Andrew-Sherwin/ECE445/Course Files/KiCAD Files/Extra Credit Video/Extra Credit Video.docx

1. Introduction/Explanation of project goal/problem statement
  a. Skit with girl saying its too humid and/or not humid enough
    i. Wow, its so dry in here
      1. Its about to get more humid later… after I turn on the humidifier *wink*
    ii. Wow its so humid in here
      1. I left the manual humidifier on, and now its 60% humidity in here
2. Highlight key operating concept(s) and features,
  a. App
    i. Manual mode, auto mode
  b. Visual aid
  c. Sensor in box, valve, fan, modular plug, cable
3. Visually demonstrate the functionality and usability of these features by showing all or a part of the device working.
  a. Showing project
4. Pull back the curtain and explain/show the guts of your project including the PCB, and any motors/sensors.
  a. Show PCBs, water level sensor, valve
