Andrew-Sherwin/ECE445/Course Files/Schematics/Block Diagram/ECE445 Block Diagram Rev2.pdf

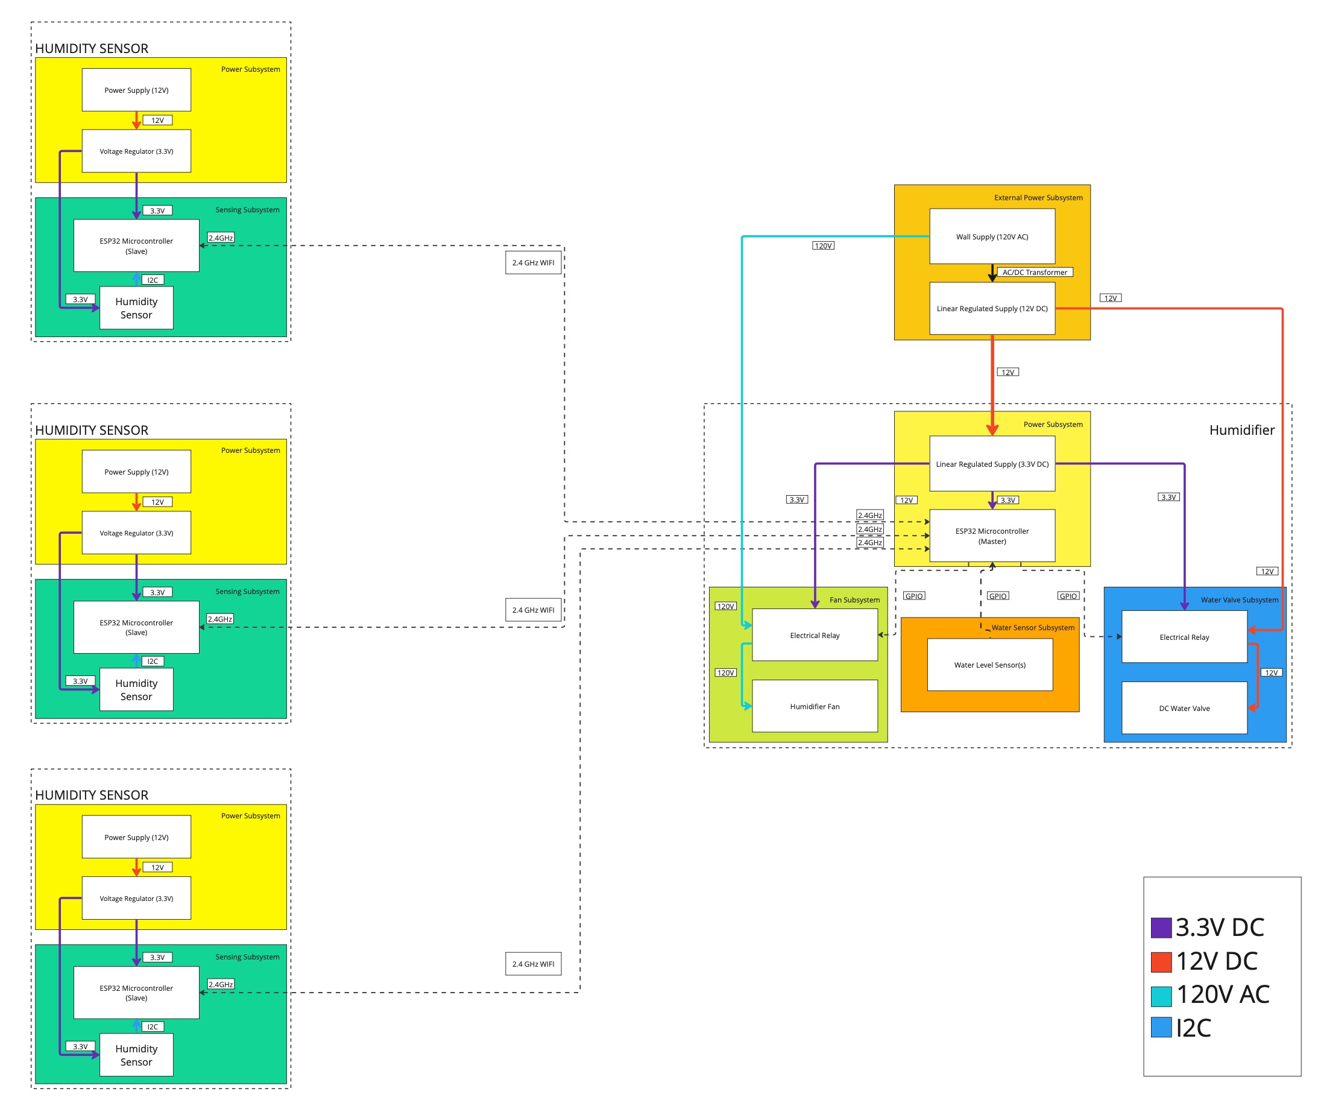
[picture p62: page 1]
