Andrew-Sherwin/ECE445/Course Files/Block Diagram/ECE445 Block Diagram Rev6.pdf

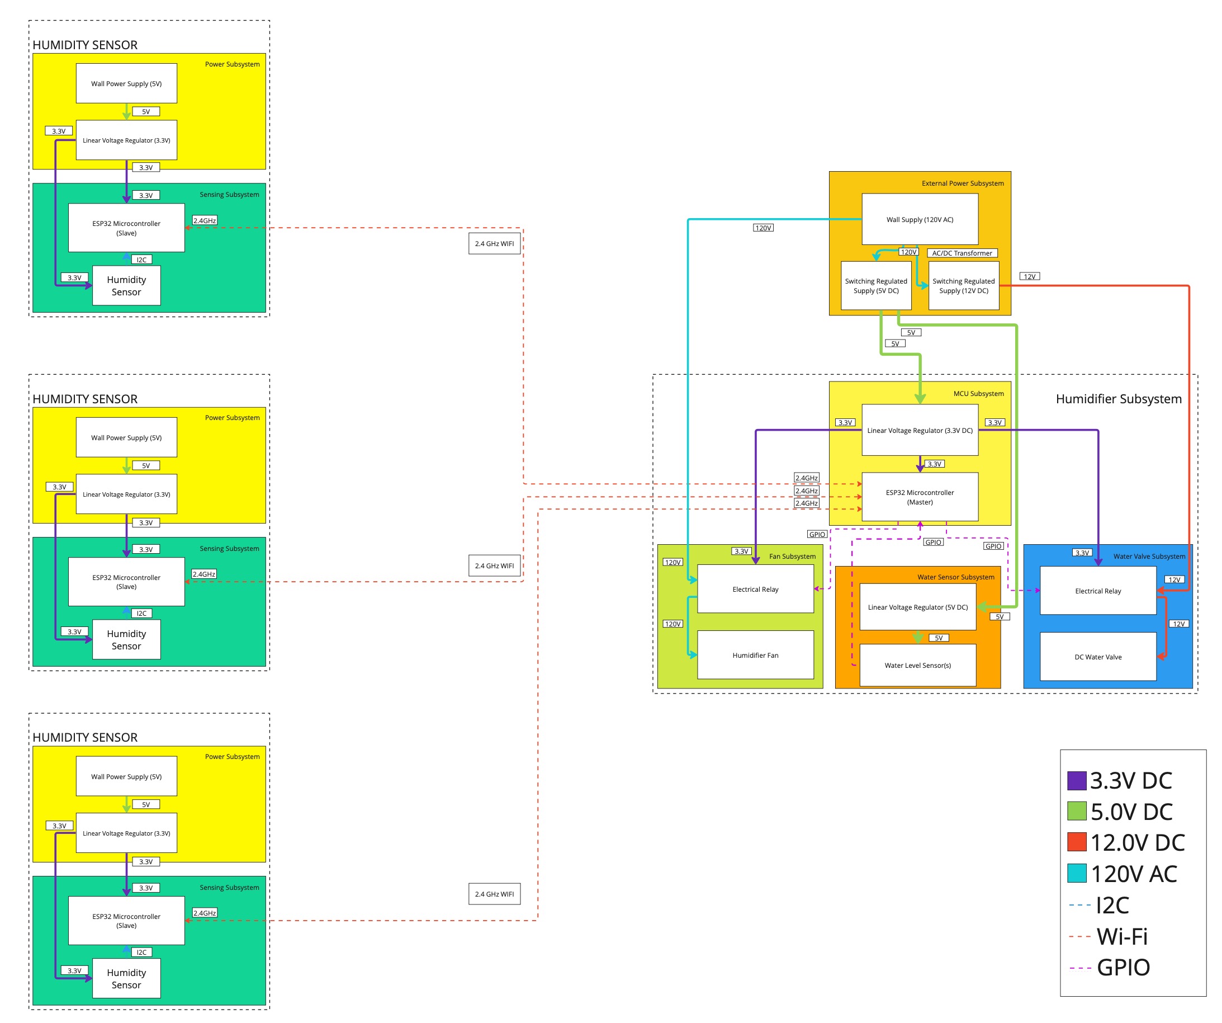
[picture p63: page 1]
