Andrew-Sherwin/ECE445/Course Files/Demonstration/Handout Rev2/Photo ECE445 Demo Handout Rev2.pdf

## Visual Aid


Automatic Humidity Sensing and Water Refilling Cool-Mist Humidifier | 5

Figure 1: Consumer Visual Aid

## Physical Design

Figure 2 – Component Visual Aid

Automatic Humidity Sensing and Water Refilling Cool-Mist Humidifier | 7

# Design

## Block Diagram


Figure 3 – Overall Block Diagram

Automatic Humidity Sensing and Water Refilling Cool-Mist Humidifier | 8


Figure 4 – Humidifier Subsystem Block Diagram (Close-up)

Automatic Humidity Sensing and Water Refilling Cool-Mist Humidifier | 9


Figure 5 – Humidity Sensor Subsystem Block Diagram (Close-up)
