Andrew-Sherwin/ECE445/Course Files/Block Diagram/ECE445 Block Diagram Rev3.pdf

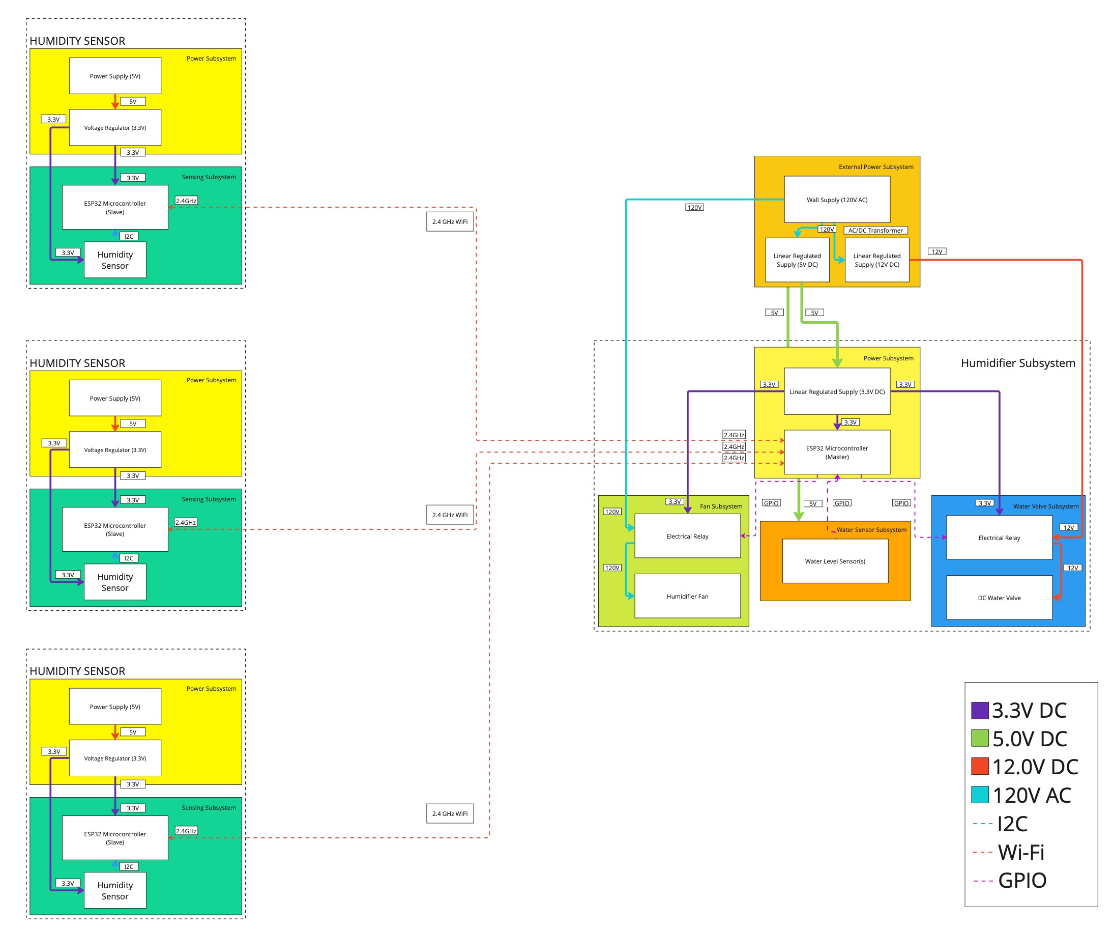
[picture p73: page 1]
