Andrew-Sherwin/ECE445/Course Files/Block Diagram/ECE445 Block Diagram Rev4.pdf

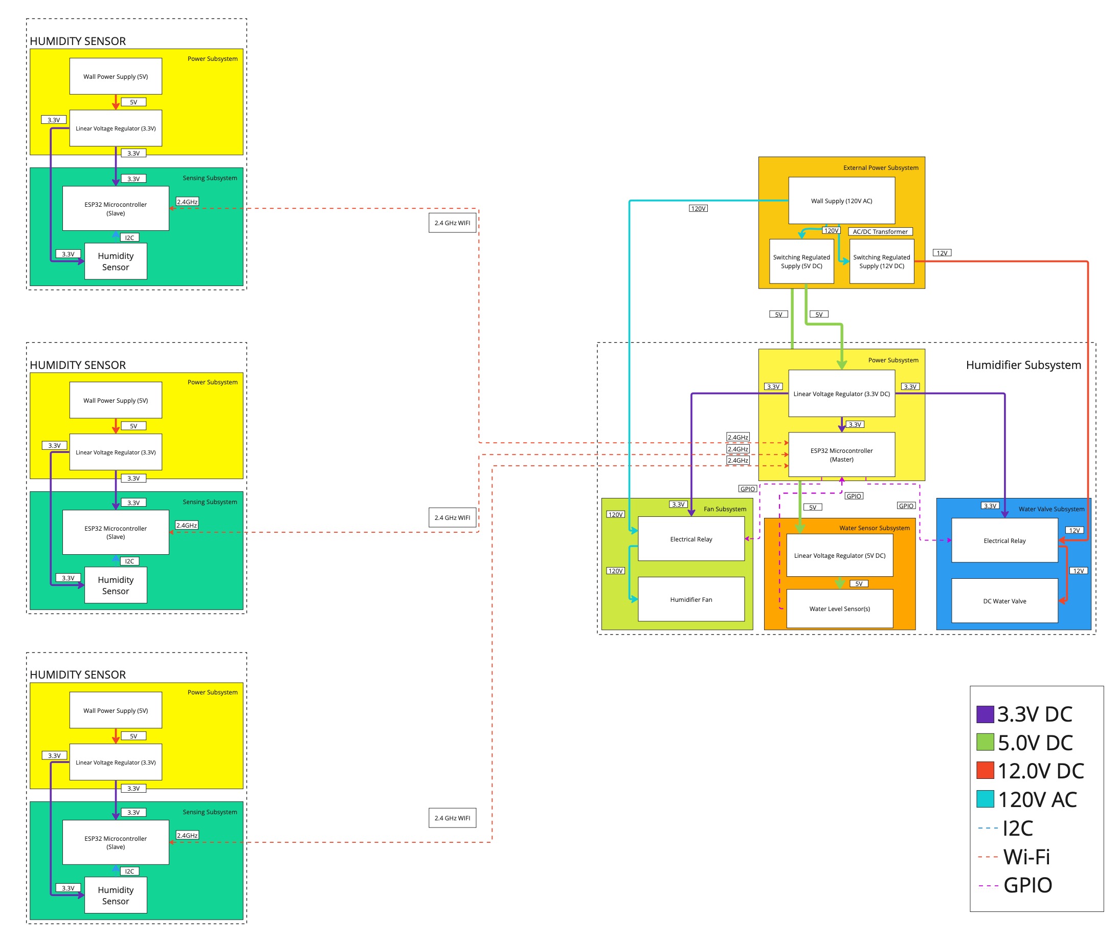
[picture p74: page 1]
