Andrew-Sherwin/ECE445/Course Files/Block Diagram/ECE445 Block Diagram Rev5.pdf

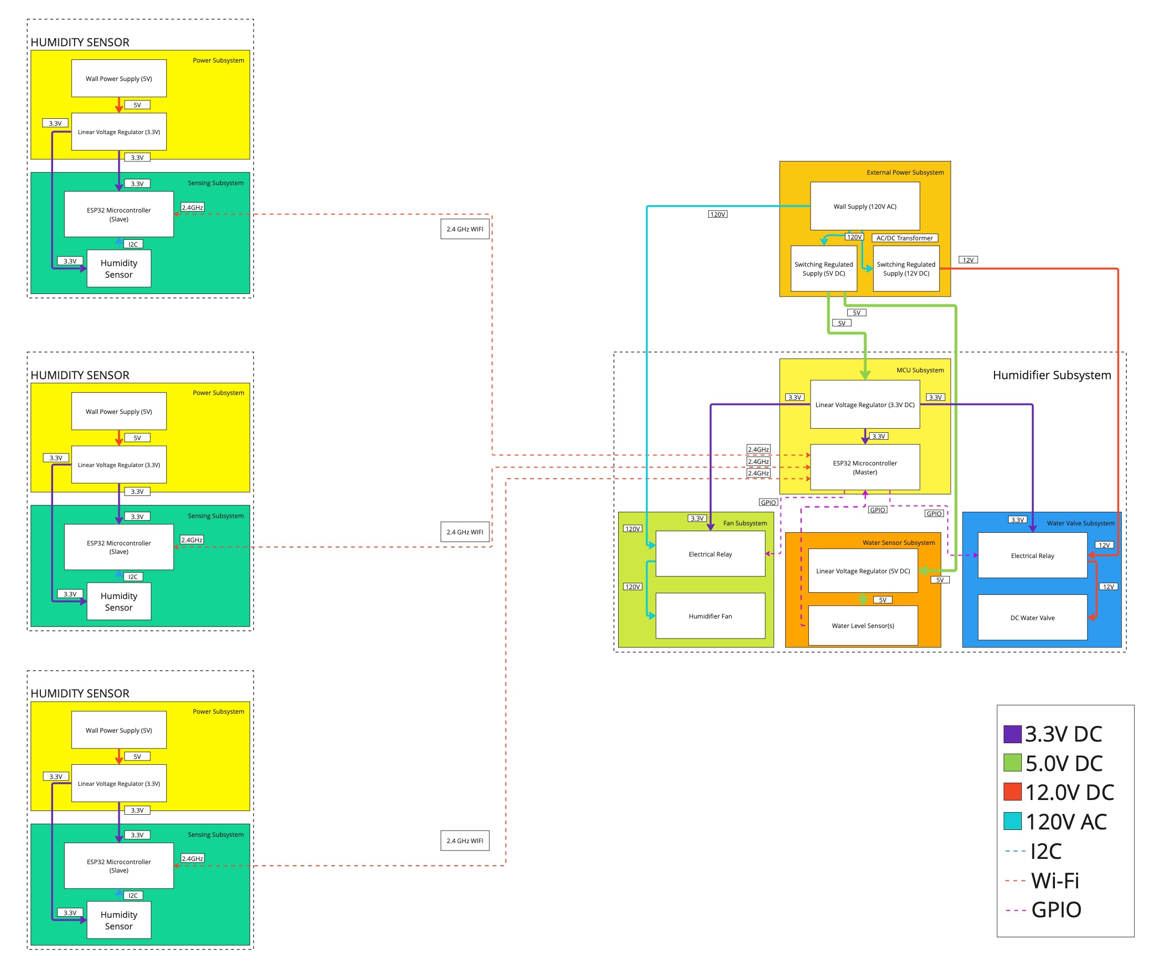
[picture p75: page 1]
