Andrew-Sherwin/ECE445/Course Files/3D Scan/humidifier photo.jpg

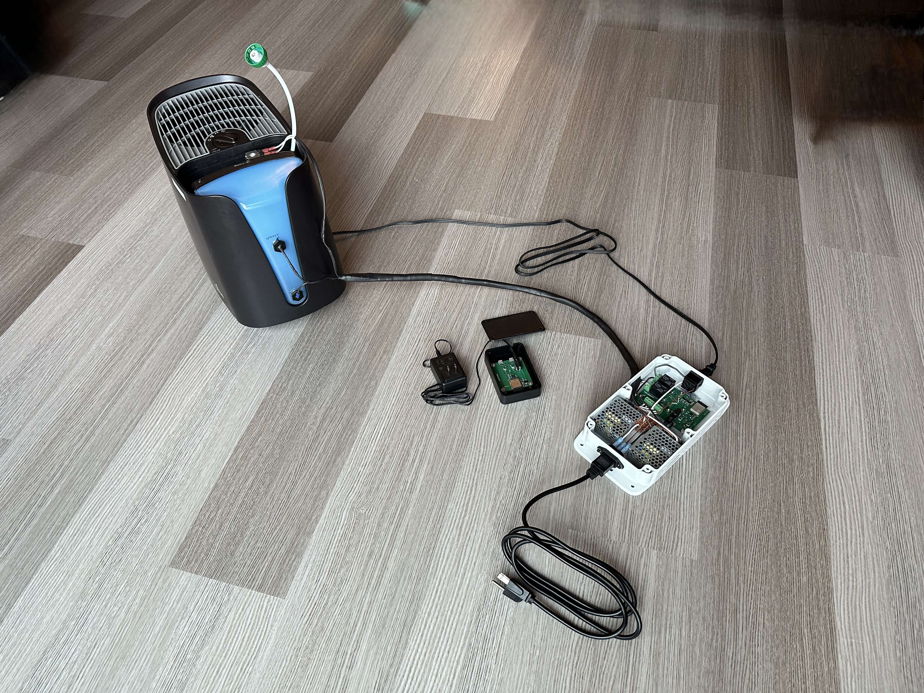
Course Files/3D Scan/humidifier photo.jpg
