Andrew-Sherwin/ECE445/Course Files/Budget/Screenshot 2024-05-01 at 22.21.20.png

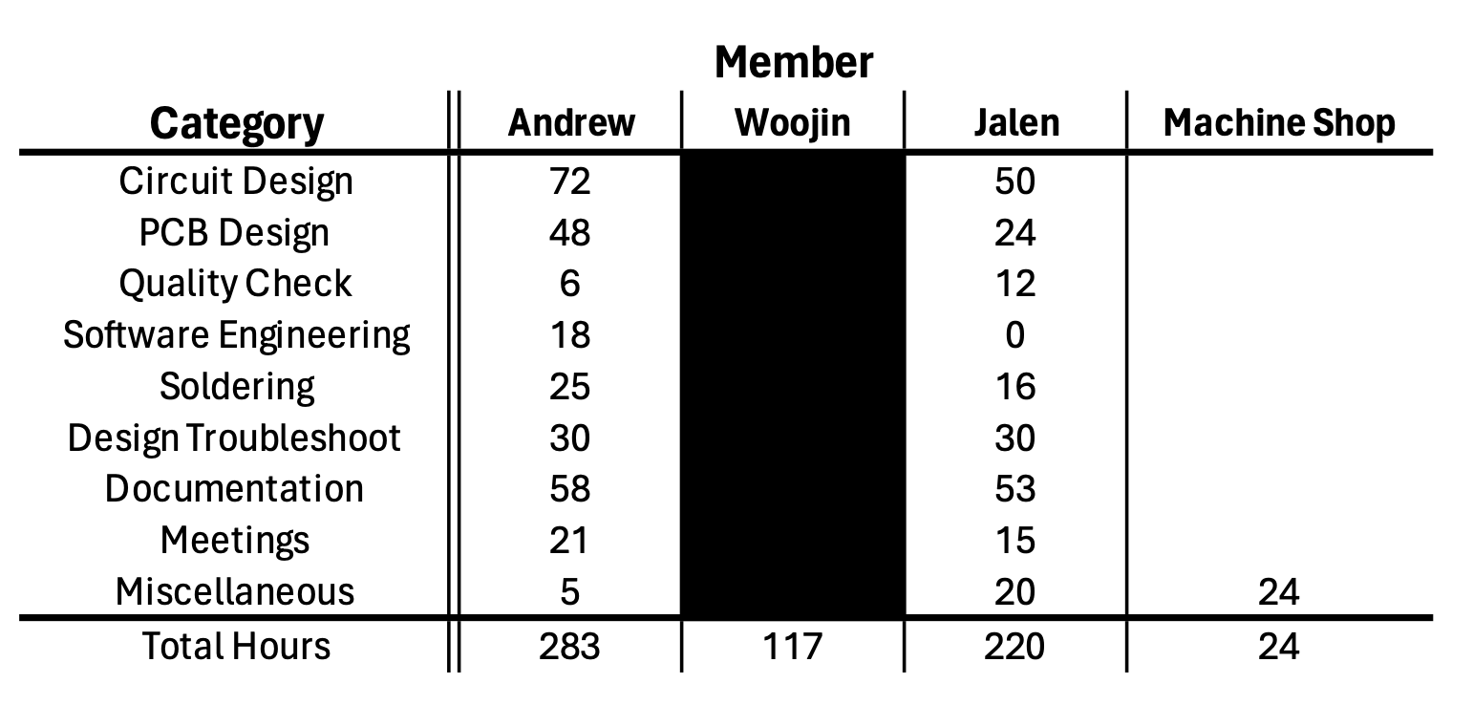
Course Files/Budget/Screenshot 2024-05-01 at 22.21.20.png
