Andrew-Sherwin/ECE445/Course Files/Demonstration/Pictures/5-1.png

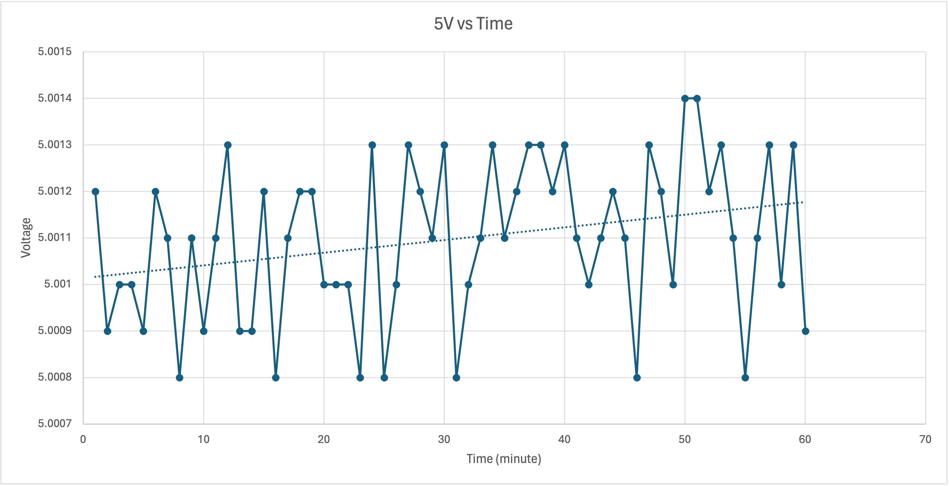
Course Files/Demonstration/Pictures/5-1.png
