Andrew-Sherwin/ECE445/Course Files/Demonstration/Pictures/5-2.png

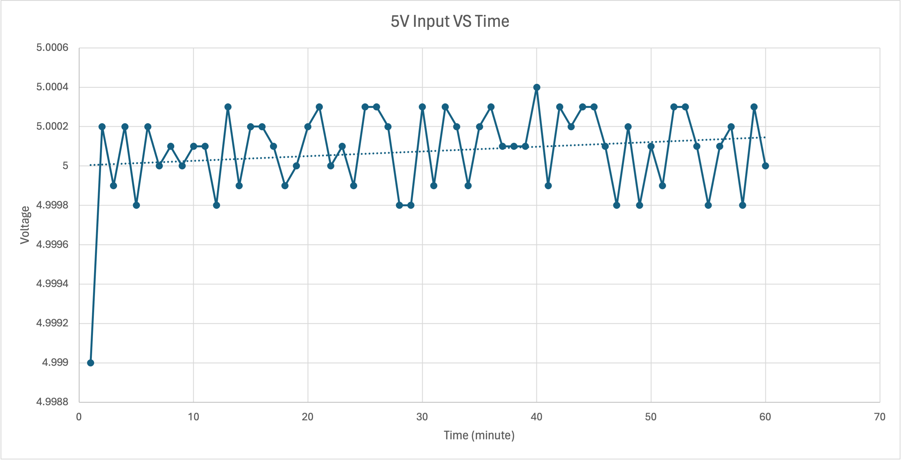
Course Files/Demonstration/Pictures/5-2.png
