Andrew-Sherwin/ECE445/Course Files/Demonstration/Pictures/33-1.png

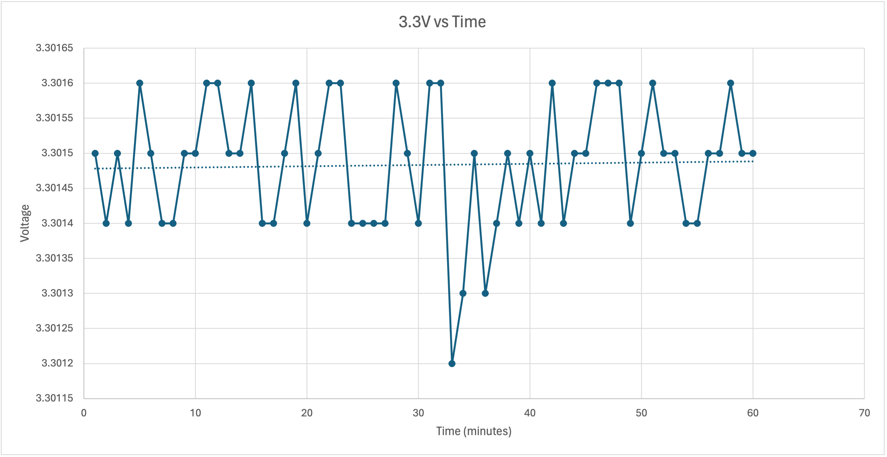
Course Files/Demonstration/Pictures/33-1.png
