Andrew-Sherwin/ECE445/Course Files/Demonstration/Pictures/33-2.png

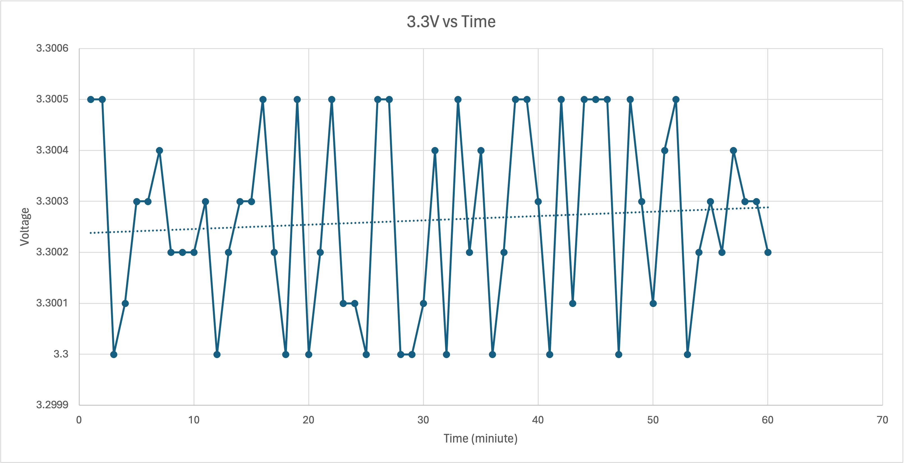
Course Files/Demonstration/Pictures/33-2.png
