Andrew-Sherwin/ECE445/Course Files/Extra Credit Video/Clips/IMG_0042.PNG

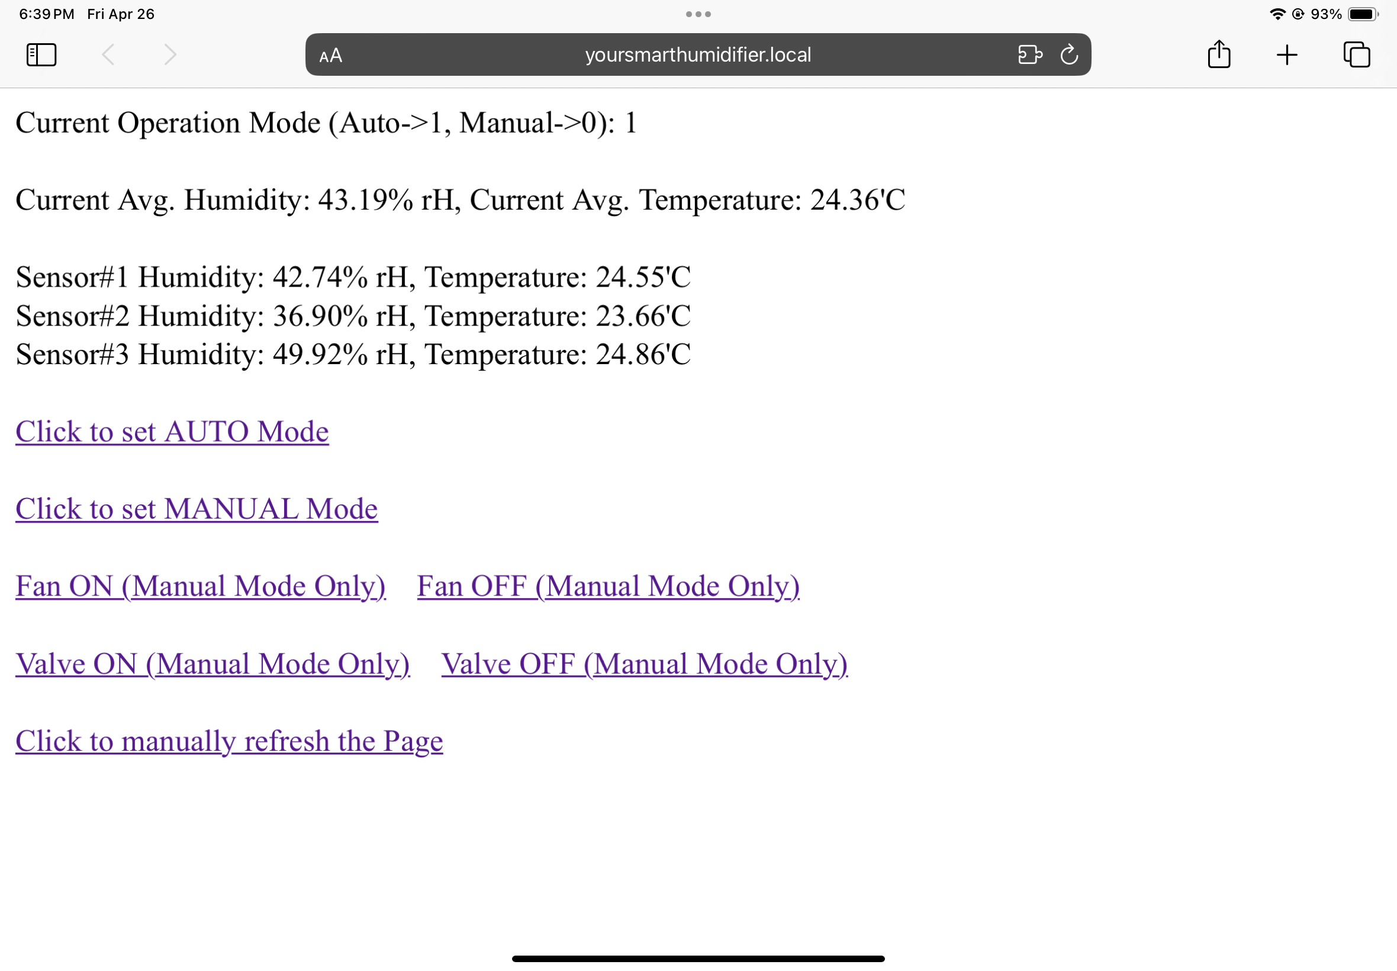
Course Files/Extra Credit Video/Clips/IMG_0042.PNG
