Andrew-Sherwin/ECE445/Course Files/Final Presentation/ebony guest.png

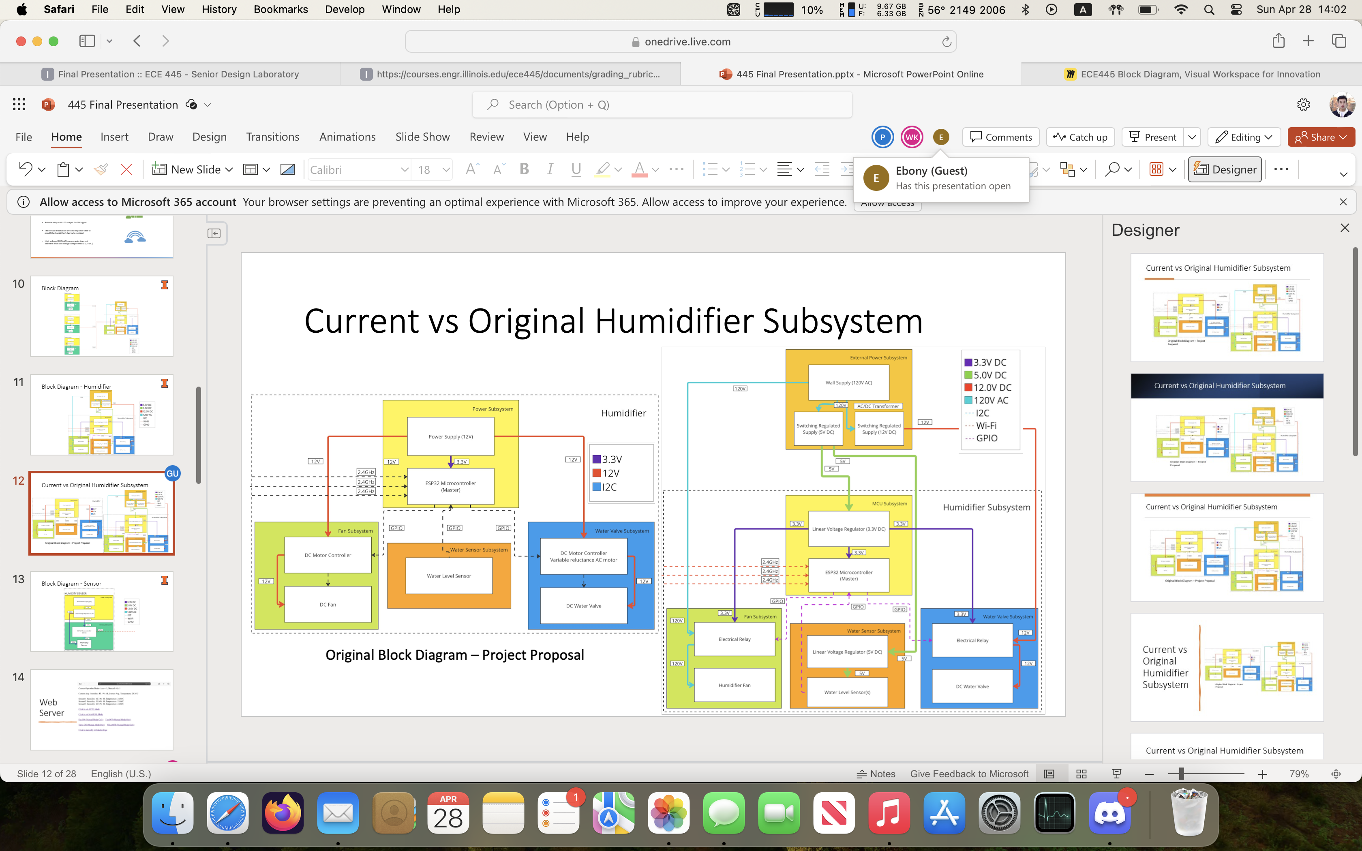
Course Files/Final Presentation/ebony guest.png
