Andrew-Sherwin/ECE445/Course Files/Final Presentation/Temp vs Time 29.1.png

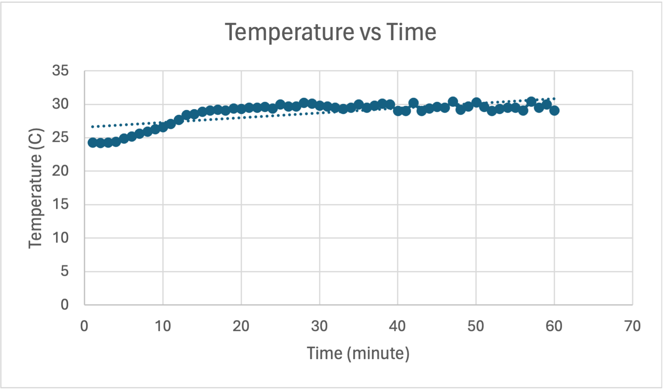
Course Files/Final Presentation/Temp vs Time 29.1.png
