Andrew-Sherwin/ECE445/Course Files/Final Presentation/Temperature vs time 311.png

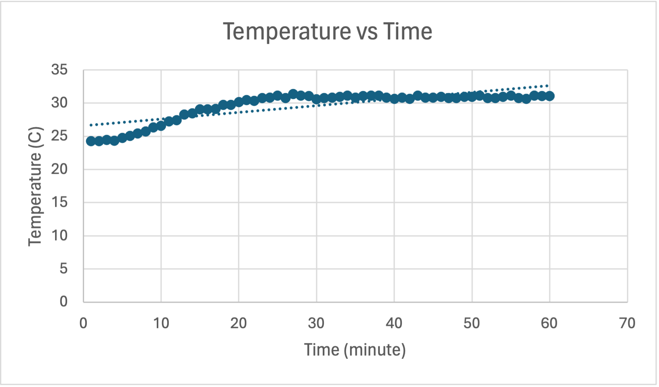
Course Files/Final Presentation/Temperature vs time 311.png
