Andrew-Sherwin/ECE445/Course Files/Final Report/Labor Table.png

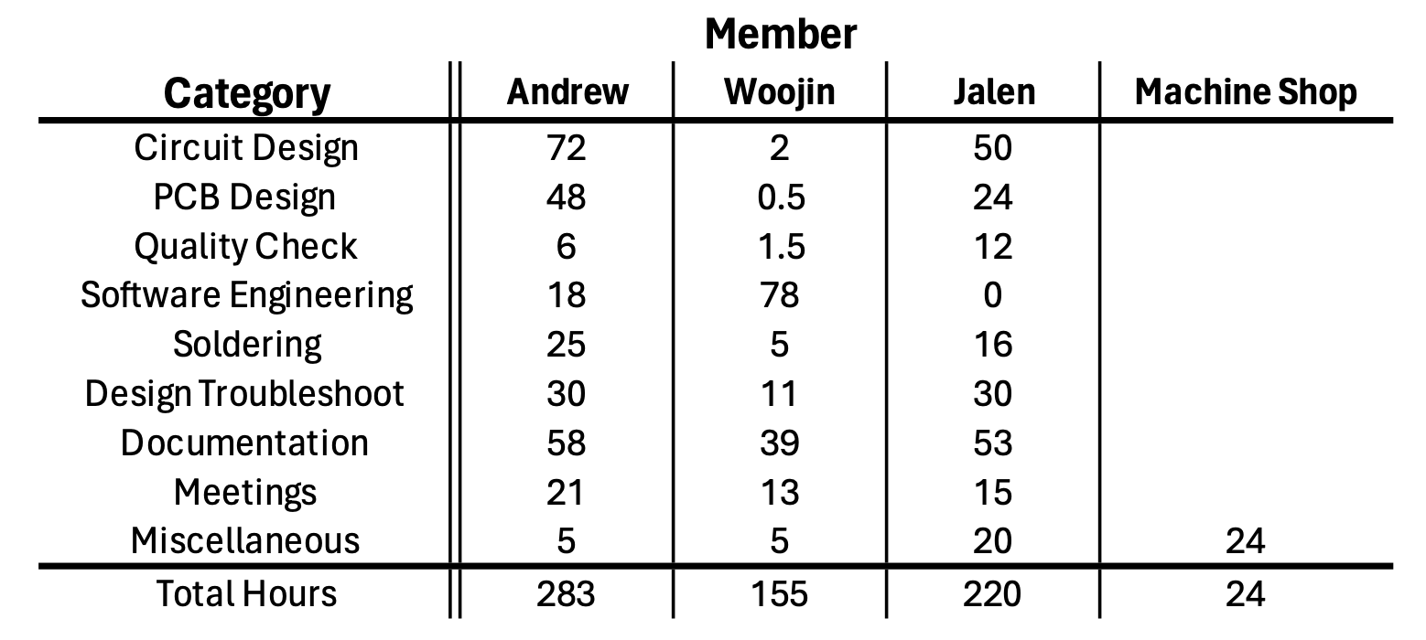
Course Files/Final Report/Labor Table.png
