Andrew-Sherwin/ECE445/Course Files/KiCAD Files/Extra Credit Video/Screenshot 2024-04-26 at 20.52.26.png

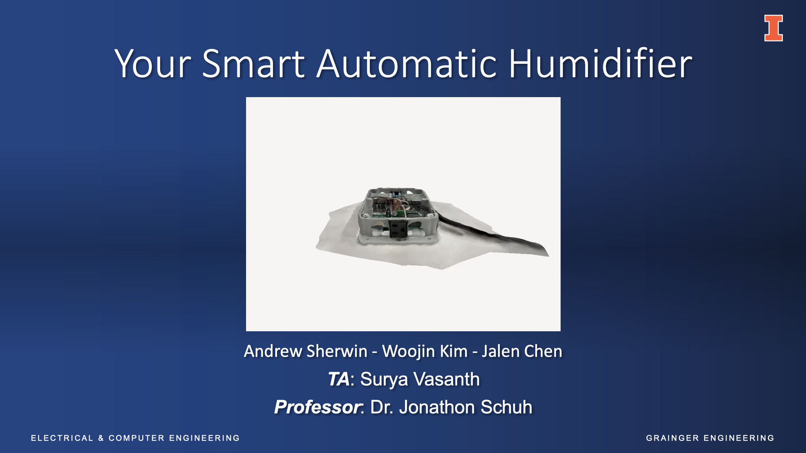
Course Files/KiCAD Files/Extra Credit Video/Screenshot 2024-04-26 at 20.52.26.png
