Andrew-Sherwin/ECE445/Course Files/KiCAD Files/Humidifier Subsystem/Jalen/Jalen kissing.png

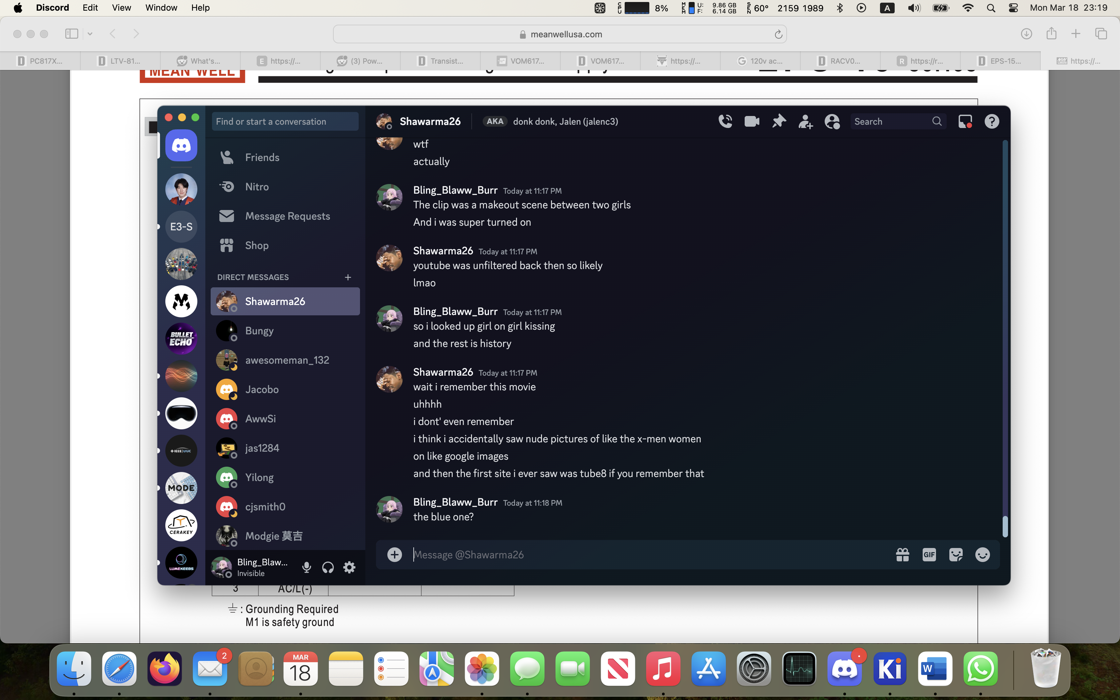
Course Files/KiCAD Files/Humidifier Subsystem/Jalen/Jalen kissing.png
