Andrew-Sherwin/ECE445/Course Files/KiCAD Files/Humidifier Subsystem/Jalen/Screenshot 2024-03-19 at 01.11.47.png

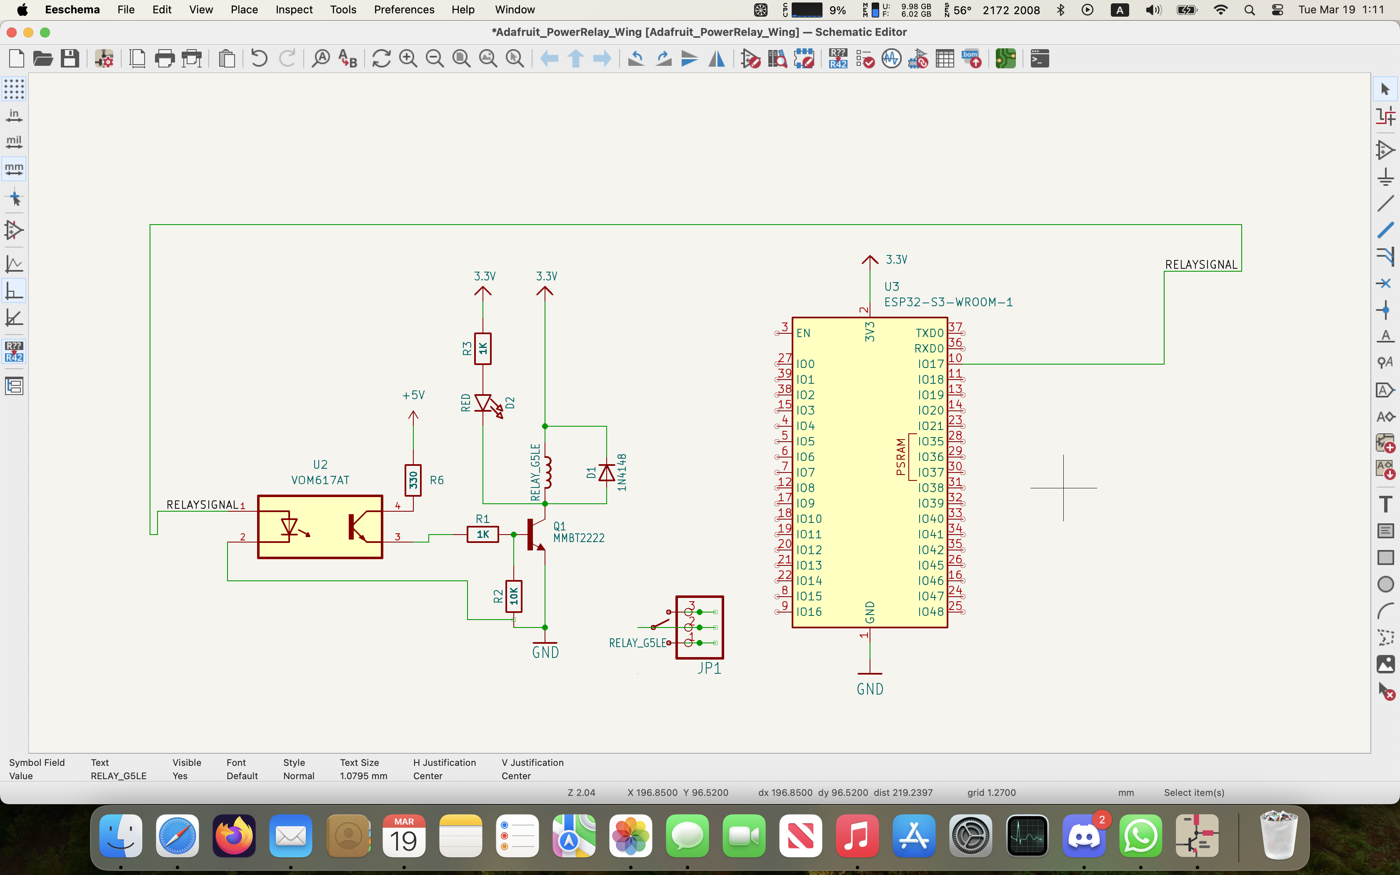
Course Files/KiCAD Files/Humidifier Subsystem/Jalen/Screenshot 2024-03-19 at 01.11.47.png
