Andrew-Sherwin/ECE445/Course Files/KiCAD Files/Humidifier Subsystem/KiCad 7.0/Rev7/Screenshot 2024-03-19 at 15.34.11.png

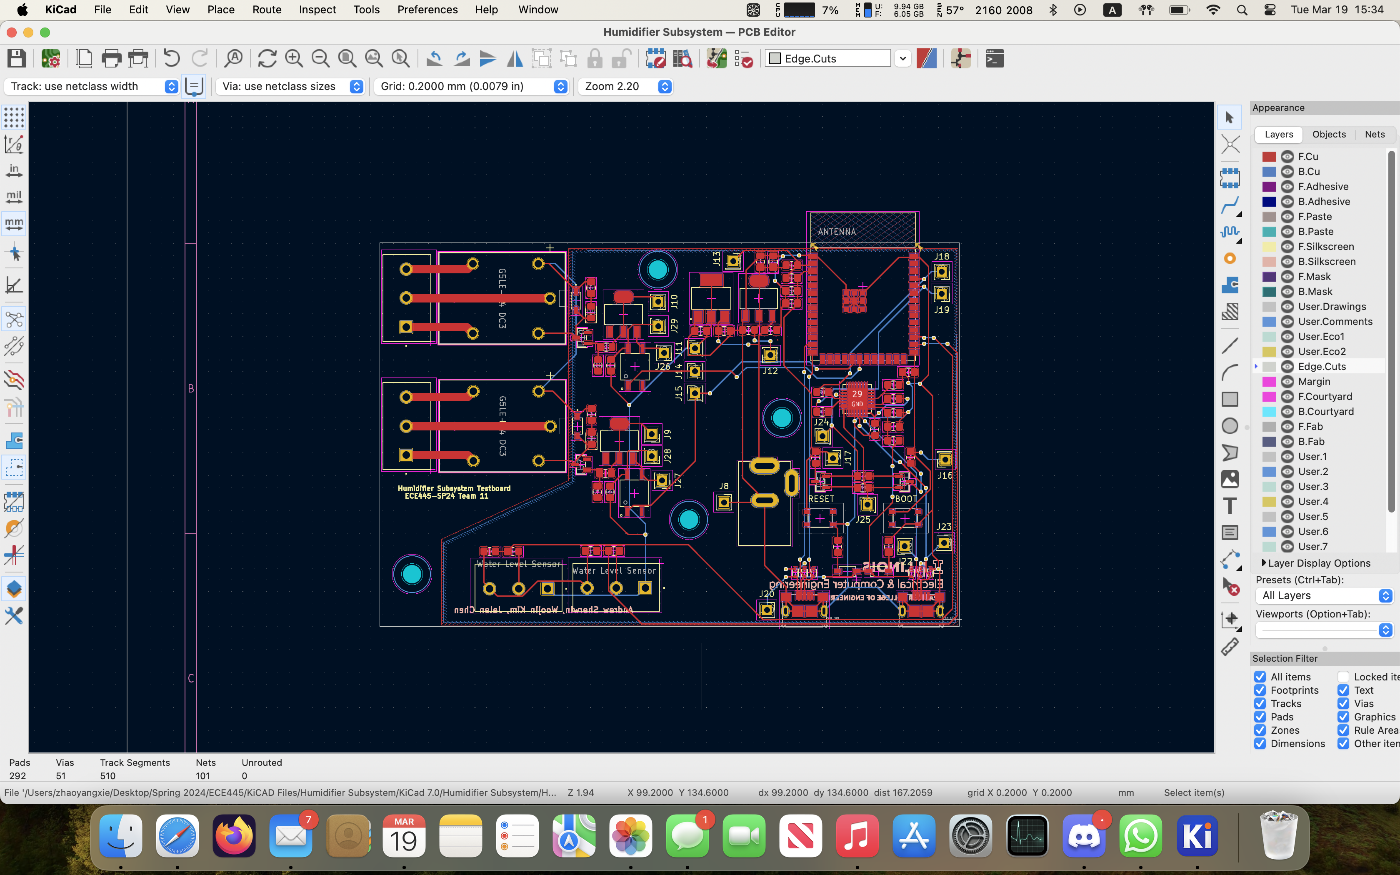
Course Files/KiCAD Files/Humidifier Subsystem/KiCad 7.0/Rev7/Screenshot 2024-03-19 at 15.34.11.png
