Andrew-Sherwin/ECE445/Course Files/KiCAD Files/Humidifier Subsystem/KiCad 7.0/Rev9 (Optocoupler Removed)/Screenshot 2024-04-07 at 02.27.28.png

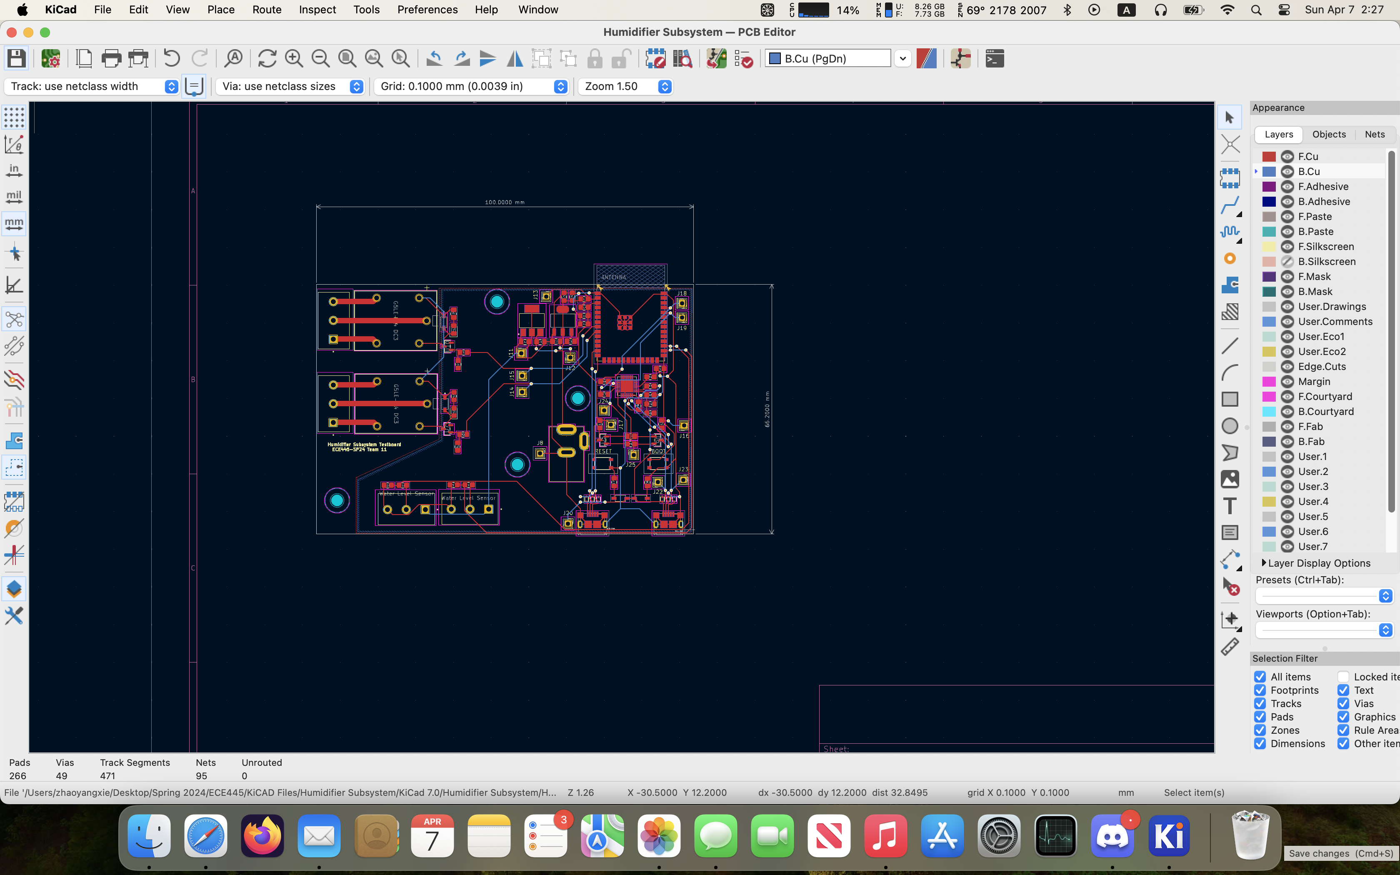
Course Files/KiCAD Files/Humidifier Subsystem/KiCad 7.0/Rev9 (Optocoupler Removed)/Screenshot 2024-04-07 at 02.27.28.png
