Andrew-Sherwin/ECE445/Course Files/KiCAD Files/Humidifier Subsystem/KiCad 7.0/Rev10 (Rerouted)/Screenshot 2024-04-07 at 06.05.55.png

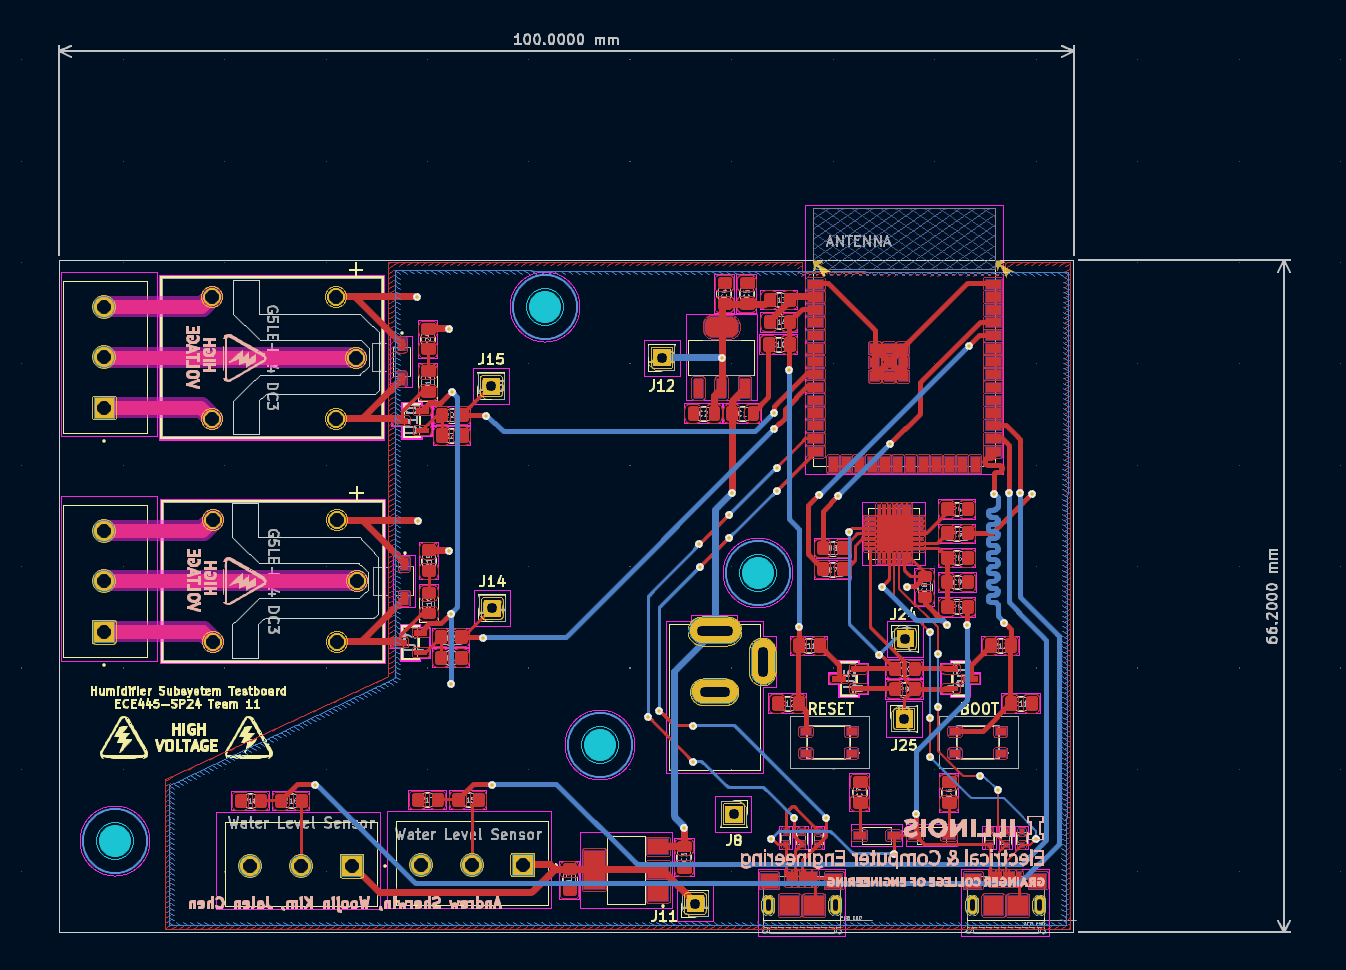
Course Files/KiCAD Files/Humidifier Subsystem/KiCad 7.0/Rev10 (Rerouted)/Screenshot 2024-04-07 at 06.05.55.png
