Andrew-Sherwin/ECE445/Course Files/KiCAD Files/Sensor Subsystem/KiCAD7.0/Rev13/Screenshot 2024-03-05 at 03.31.21.png

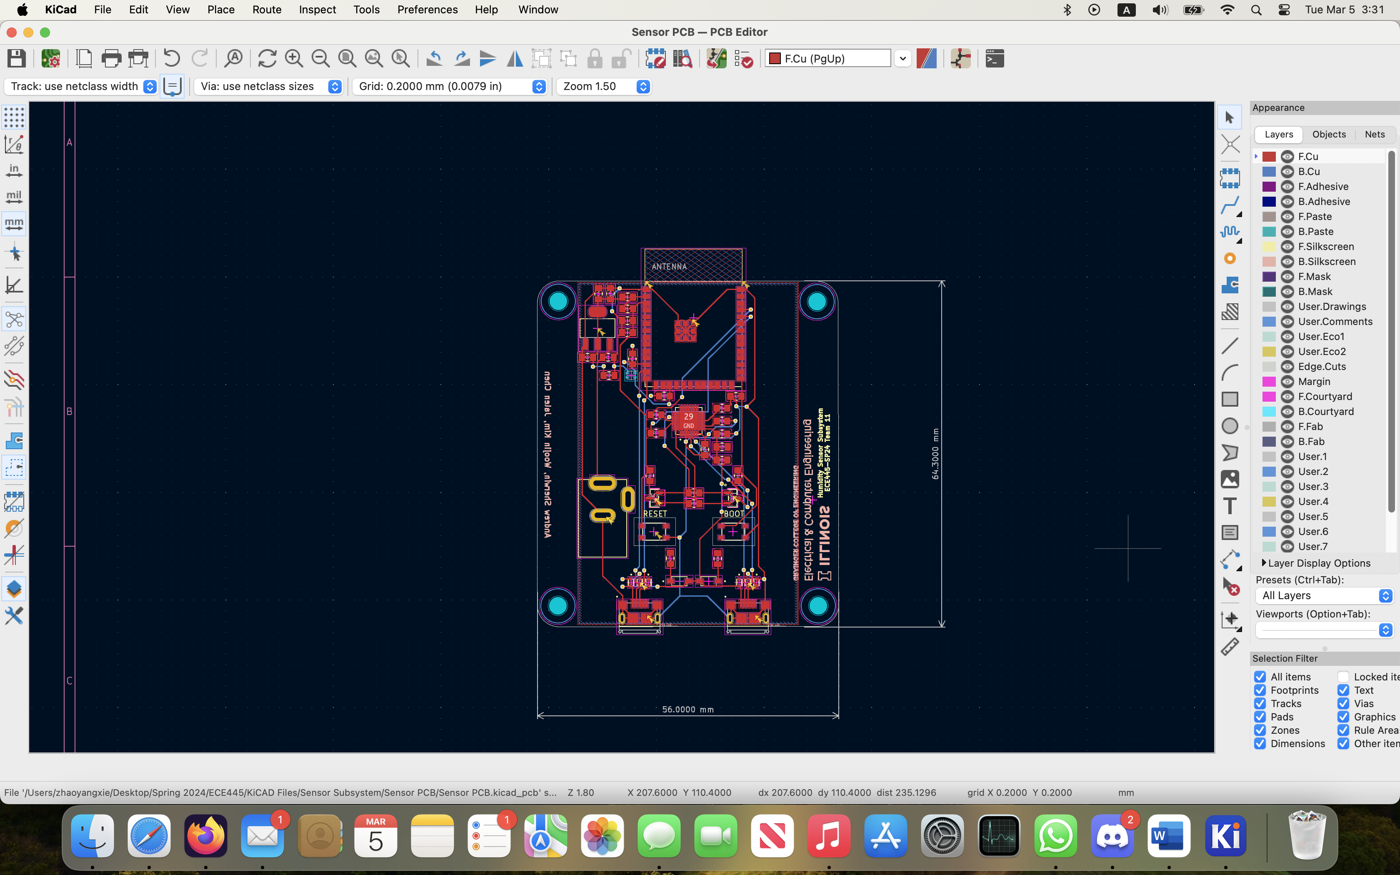
Course Files/KiCAD Files/Sensor Subsystem/KiCAD7.0/Rev13/Screenshot 2024-03-05 at 03.31.21.png
