Andrew-Sherwin/ECE445/Course Files/Proposal/Block Diagram V1.png

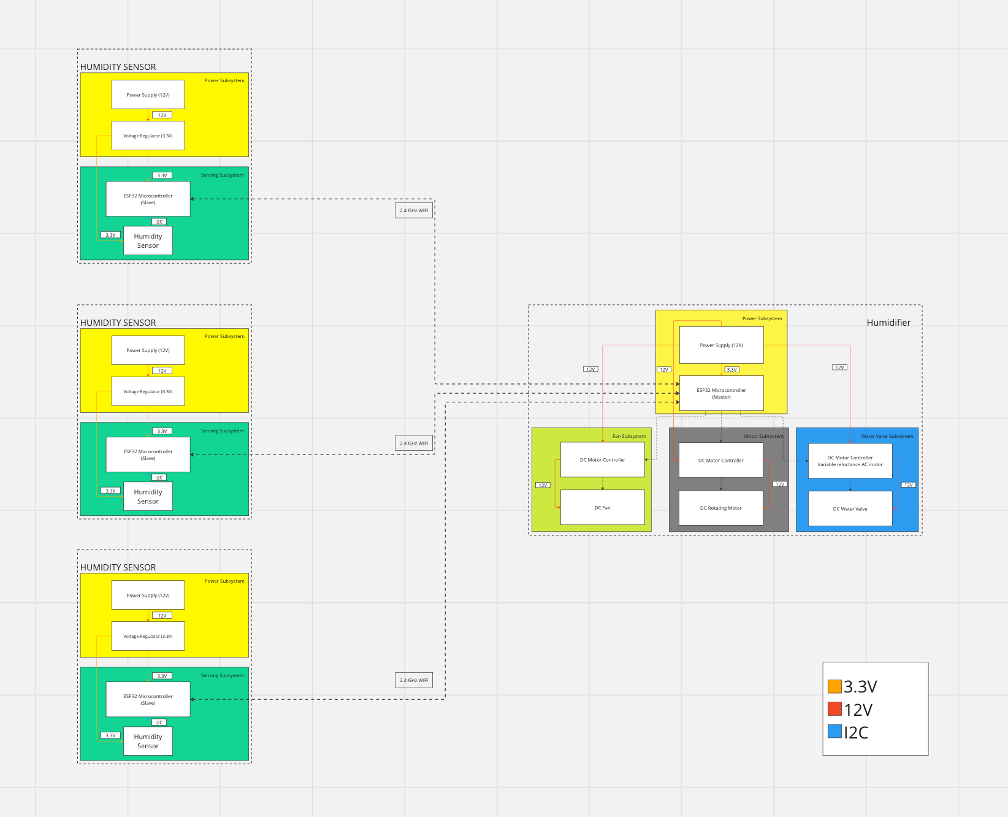
Course Files/Proposal/Block Diagram V1.png
