Andrew-Sherwin/ECE445/Course Files/Schematics/V1/With Labels/Sensor PCB.pdf

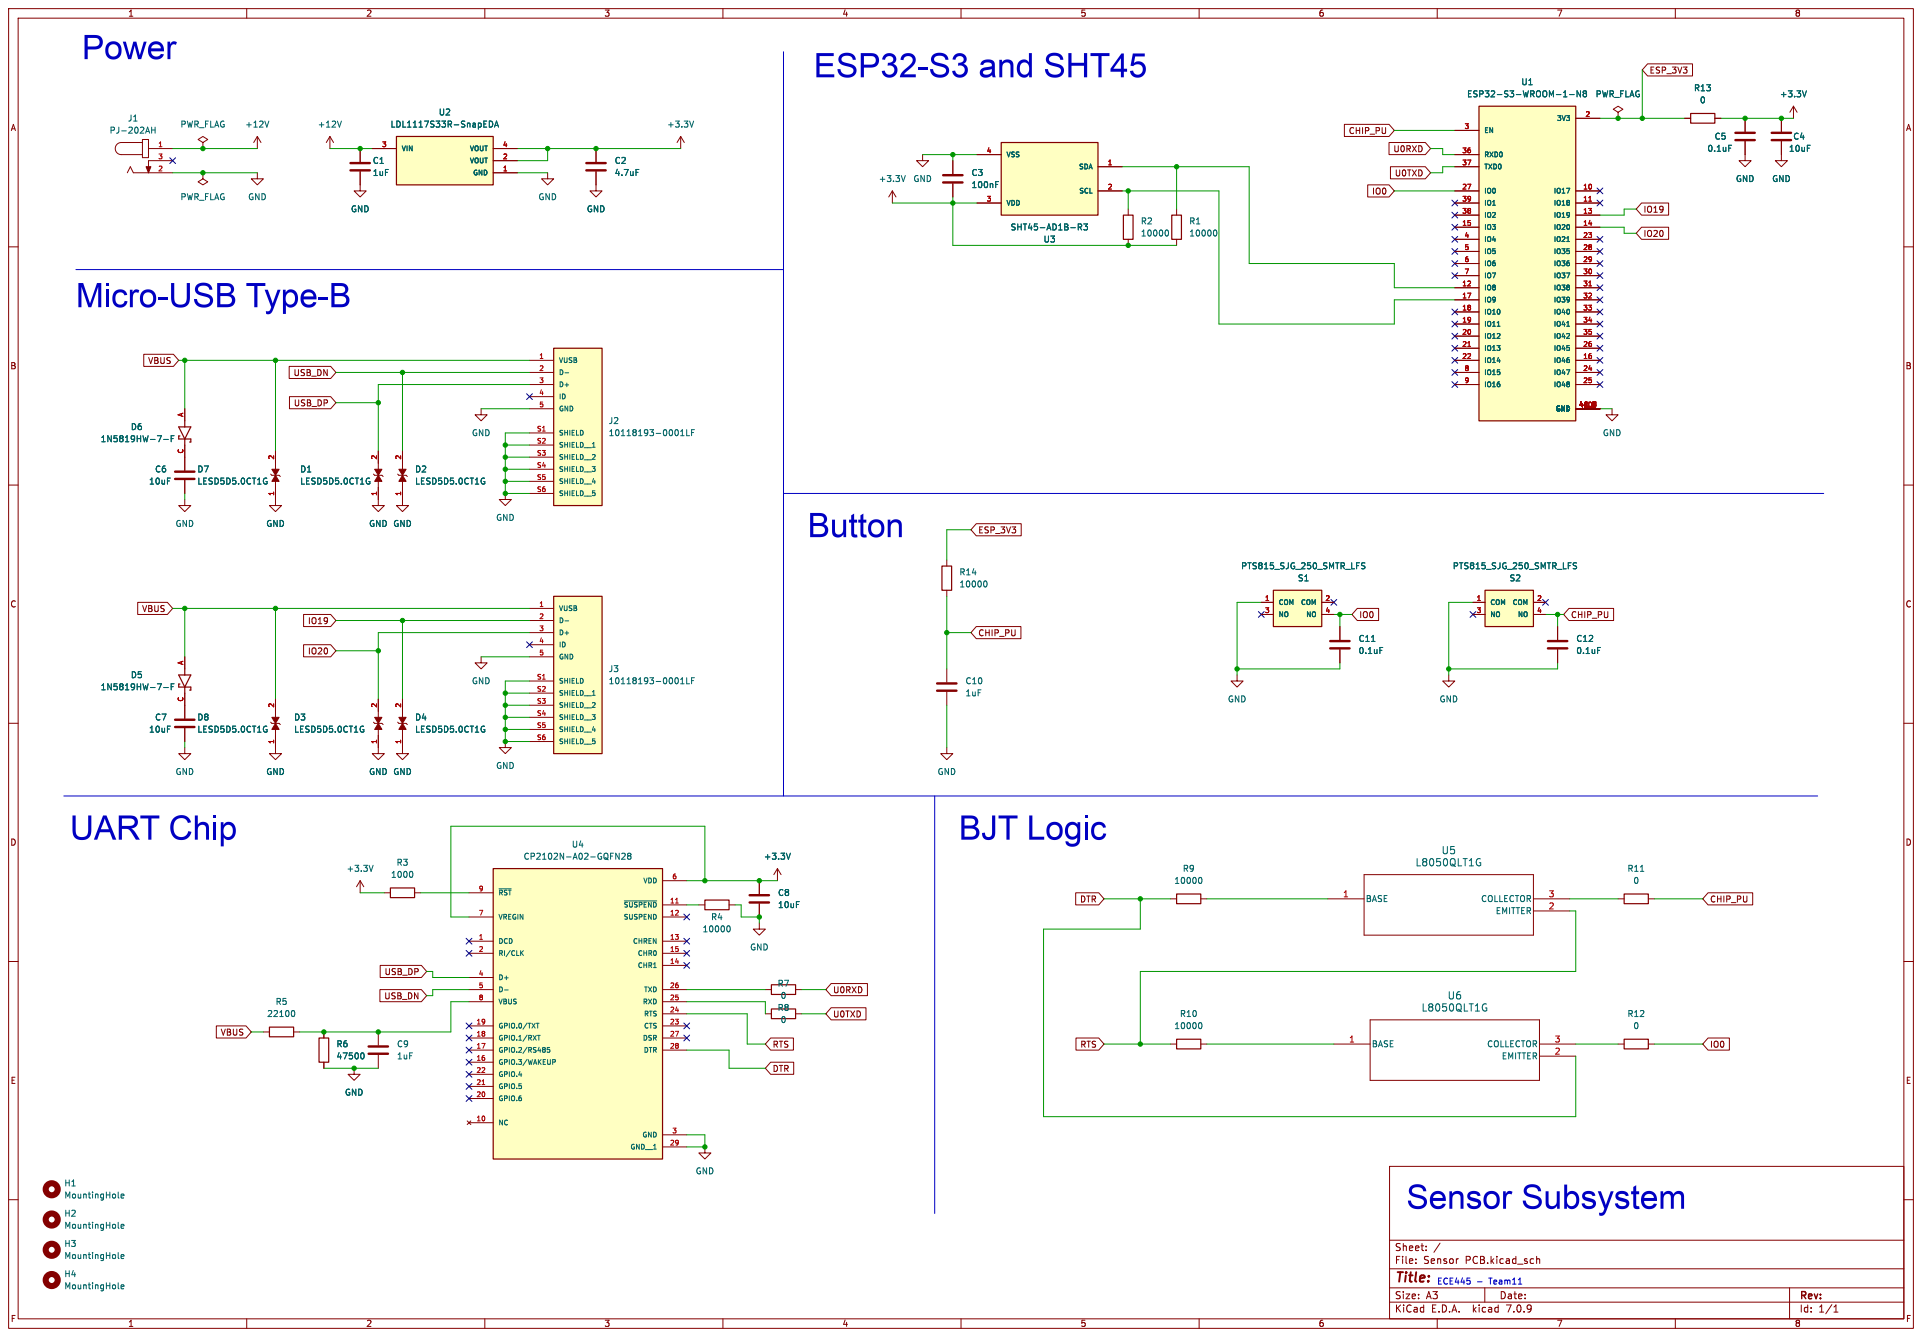
[picture p157: page 1]

H4 MountingHole H3 MountingHole H1 MountingHole H2 MountingHole
