Andrew-Sherwin/ECE445/Course Files/KiCAD Files/Humidifier Subsystem/KiCad 7.0/Rev7/Humidifier Subsystem Rev7.pdf

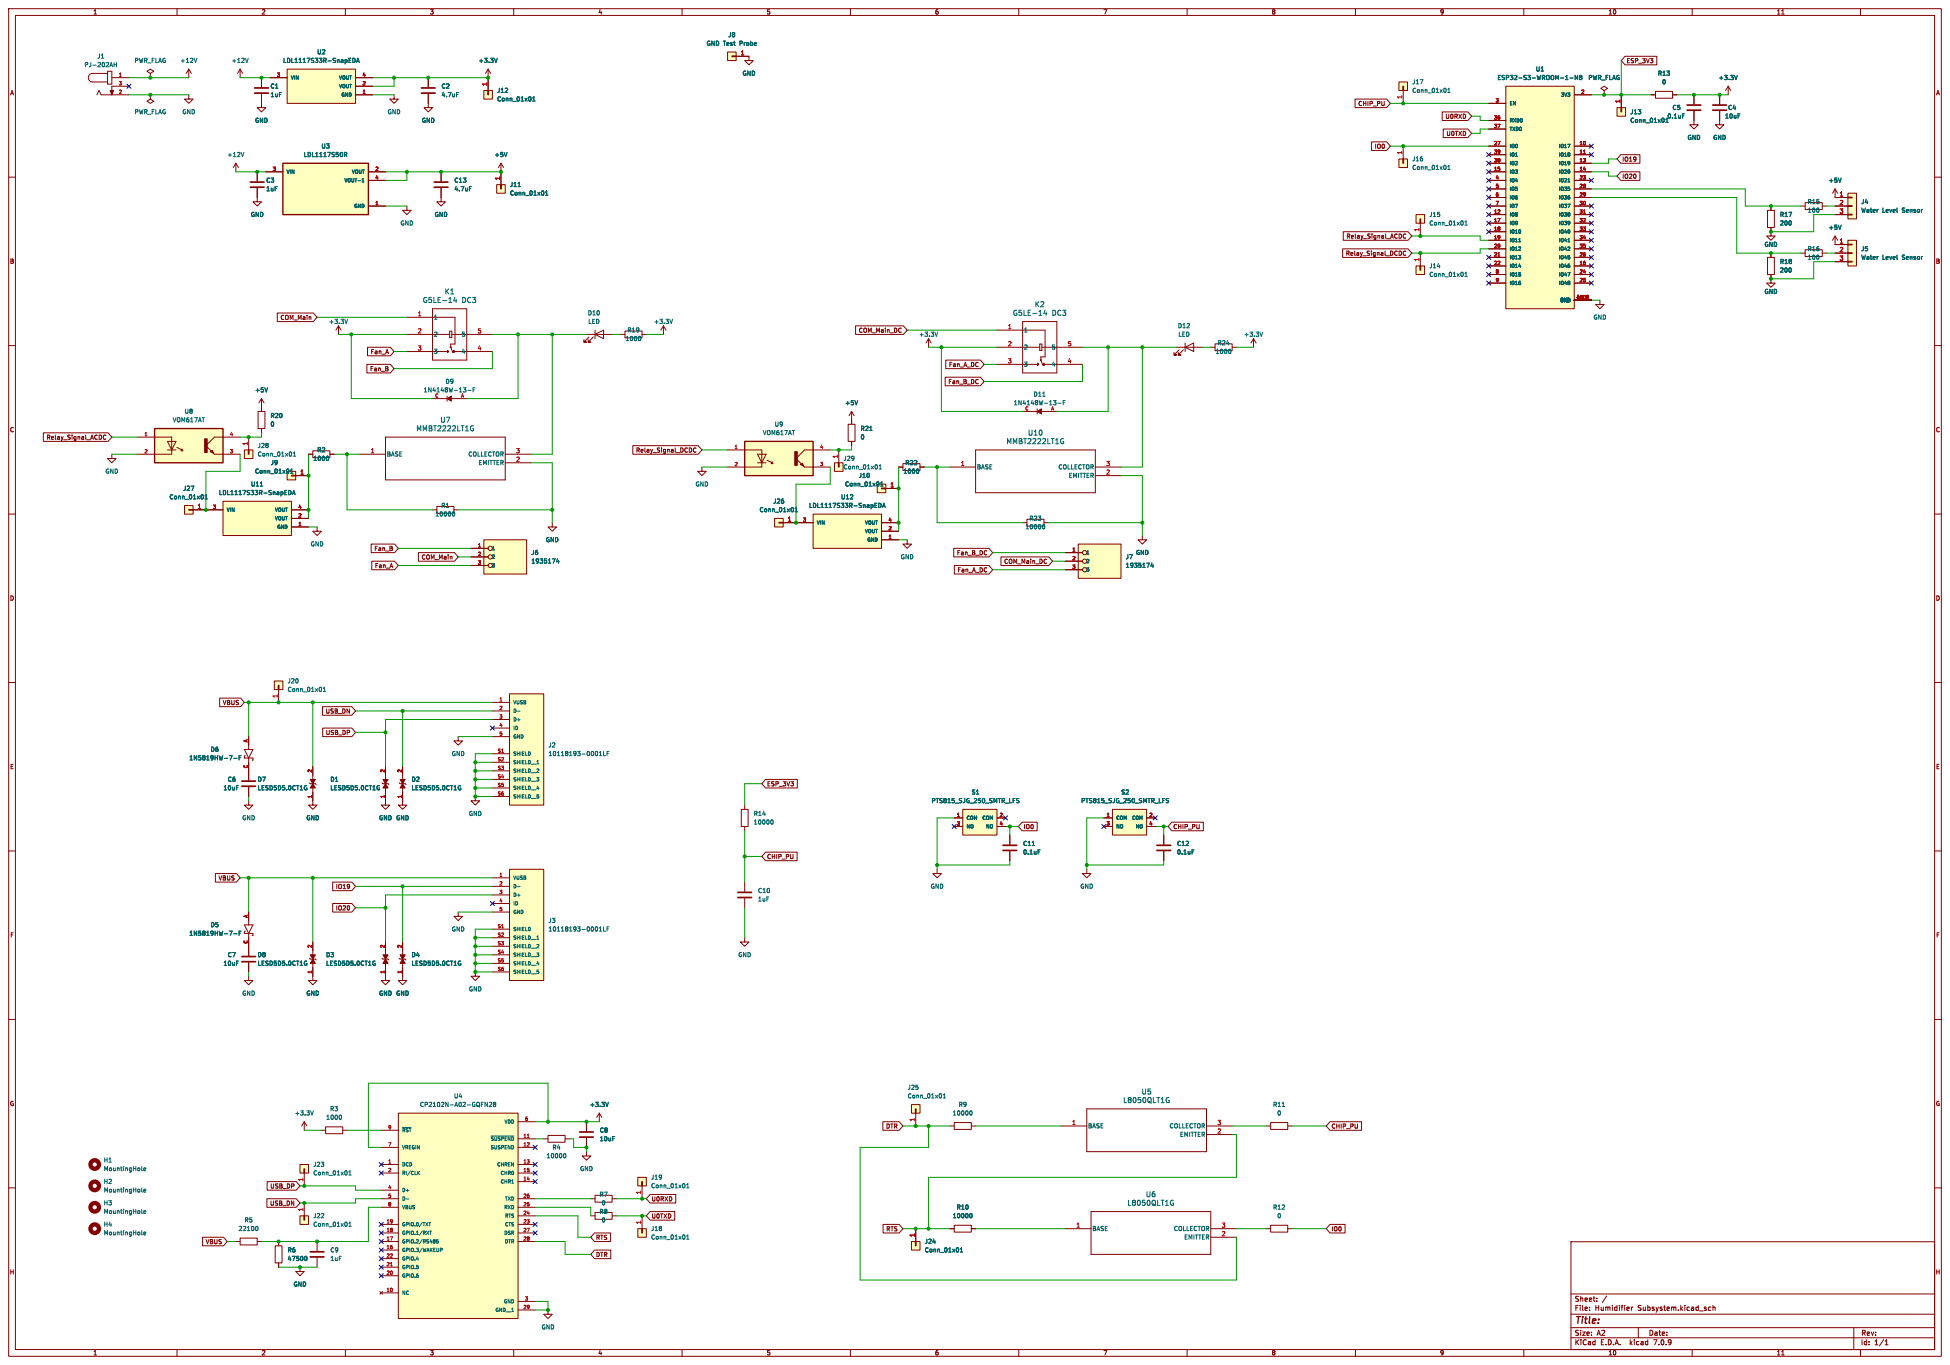
[picture p158: page 1]

J8 GND Test Probe GND
