Andrew-Sherwin/ECE445/Course Files/Humidifier Top Level.pdf

# Humidifier Top Level

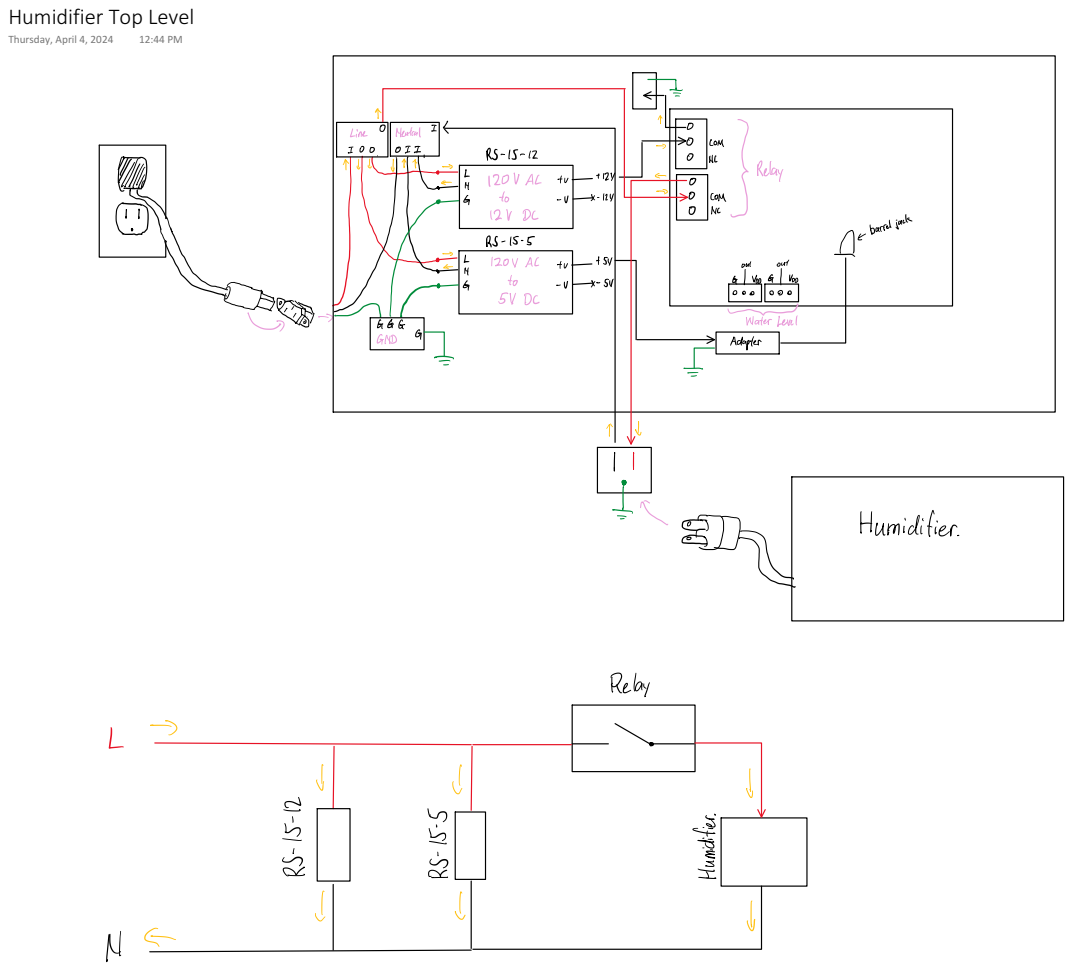
[picture p160: page 1]
Thursday, April 4, 2024
