Andrew-Sherwin/ECE445/Course Files/KiCAD Files/Humidifier Subsystem/KiCad 7.0/Rev3/Humidifier Subsystem Rev3.pdf

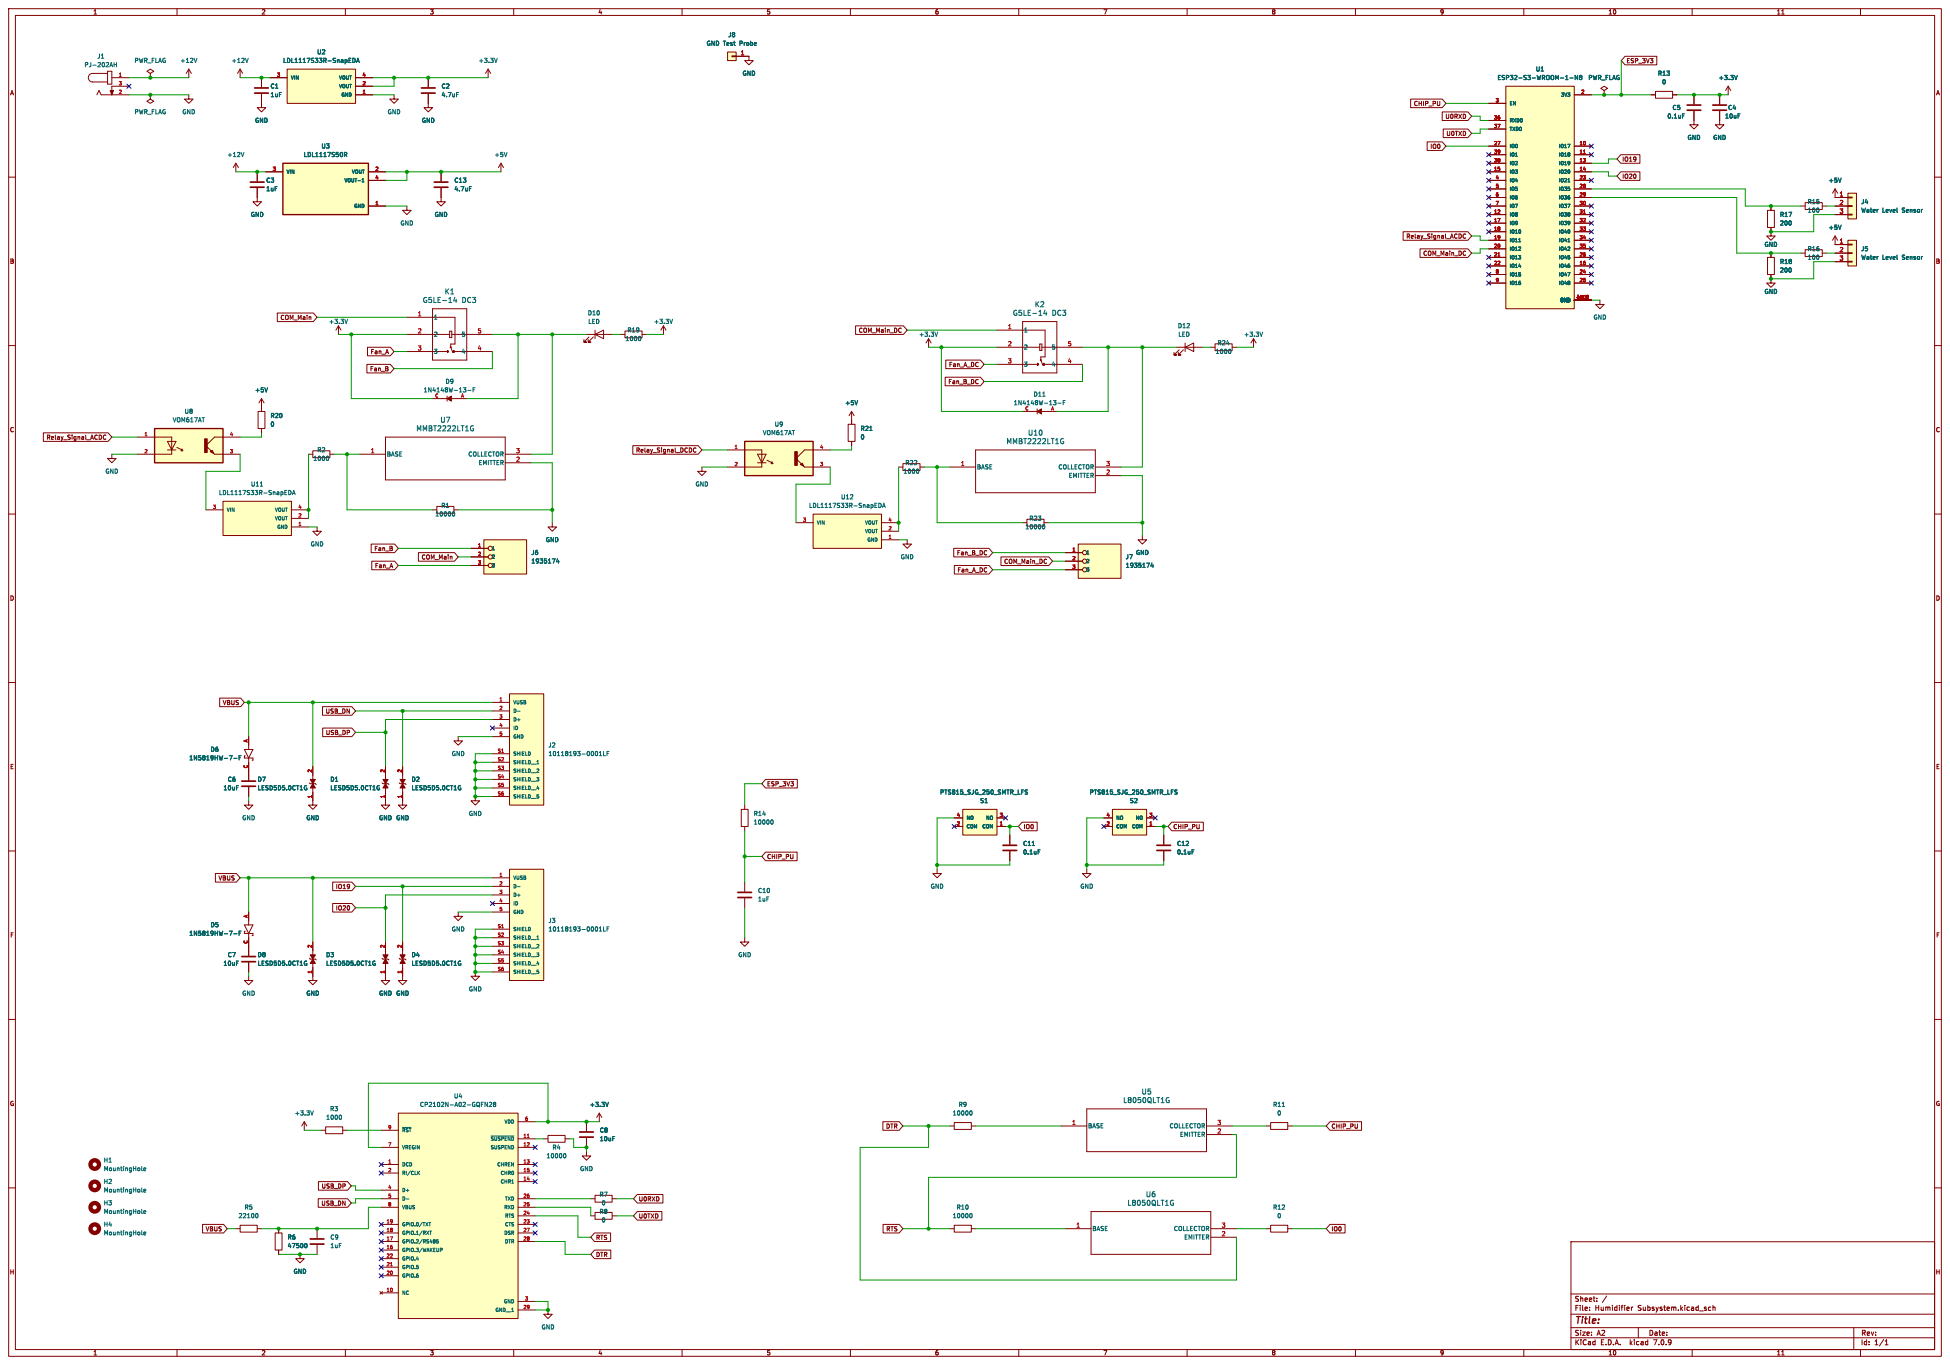
[picture p161: page 1]

J8 GND Test Probe GND
