Andrew-Sherwin/ECE445/Course Files/KiCAD Files/Humidifier Subsystem/KiCad 7.0/Rev4/Humidifier Subsystem Rev4 with 1x1.pdf

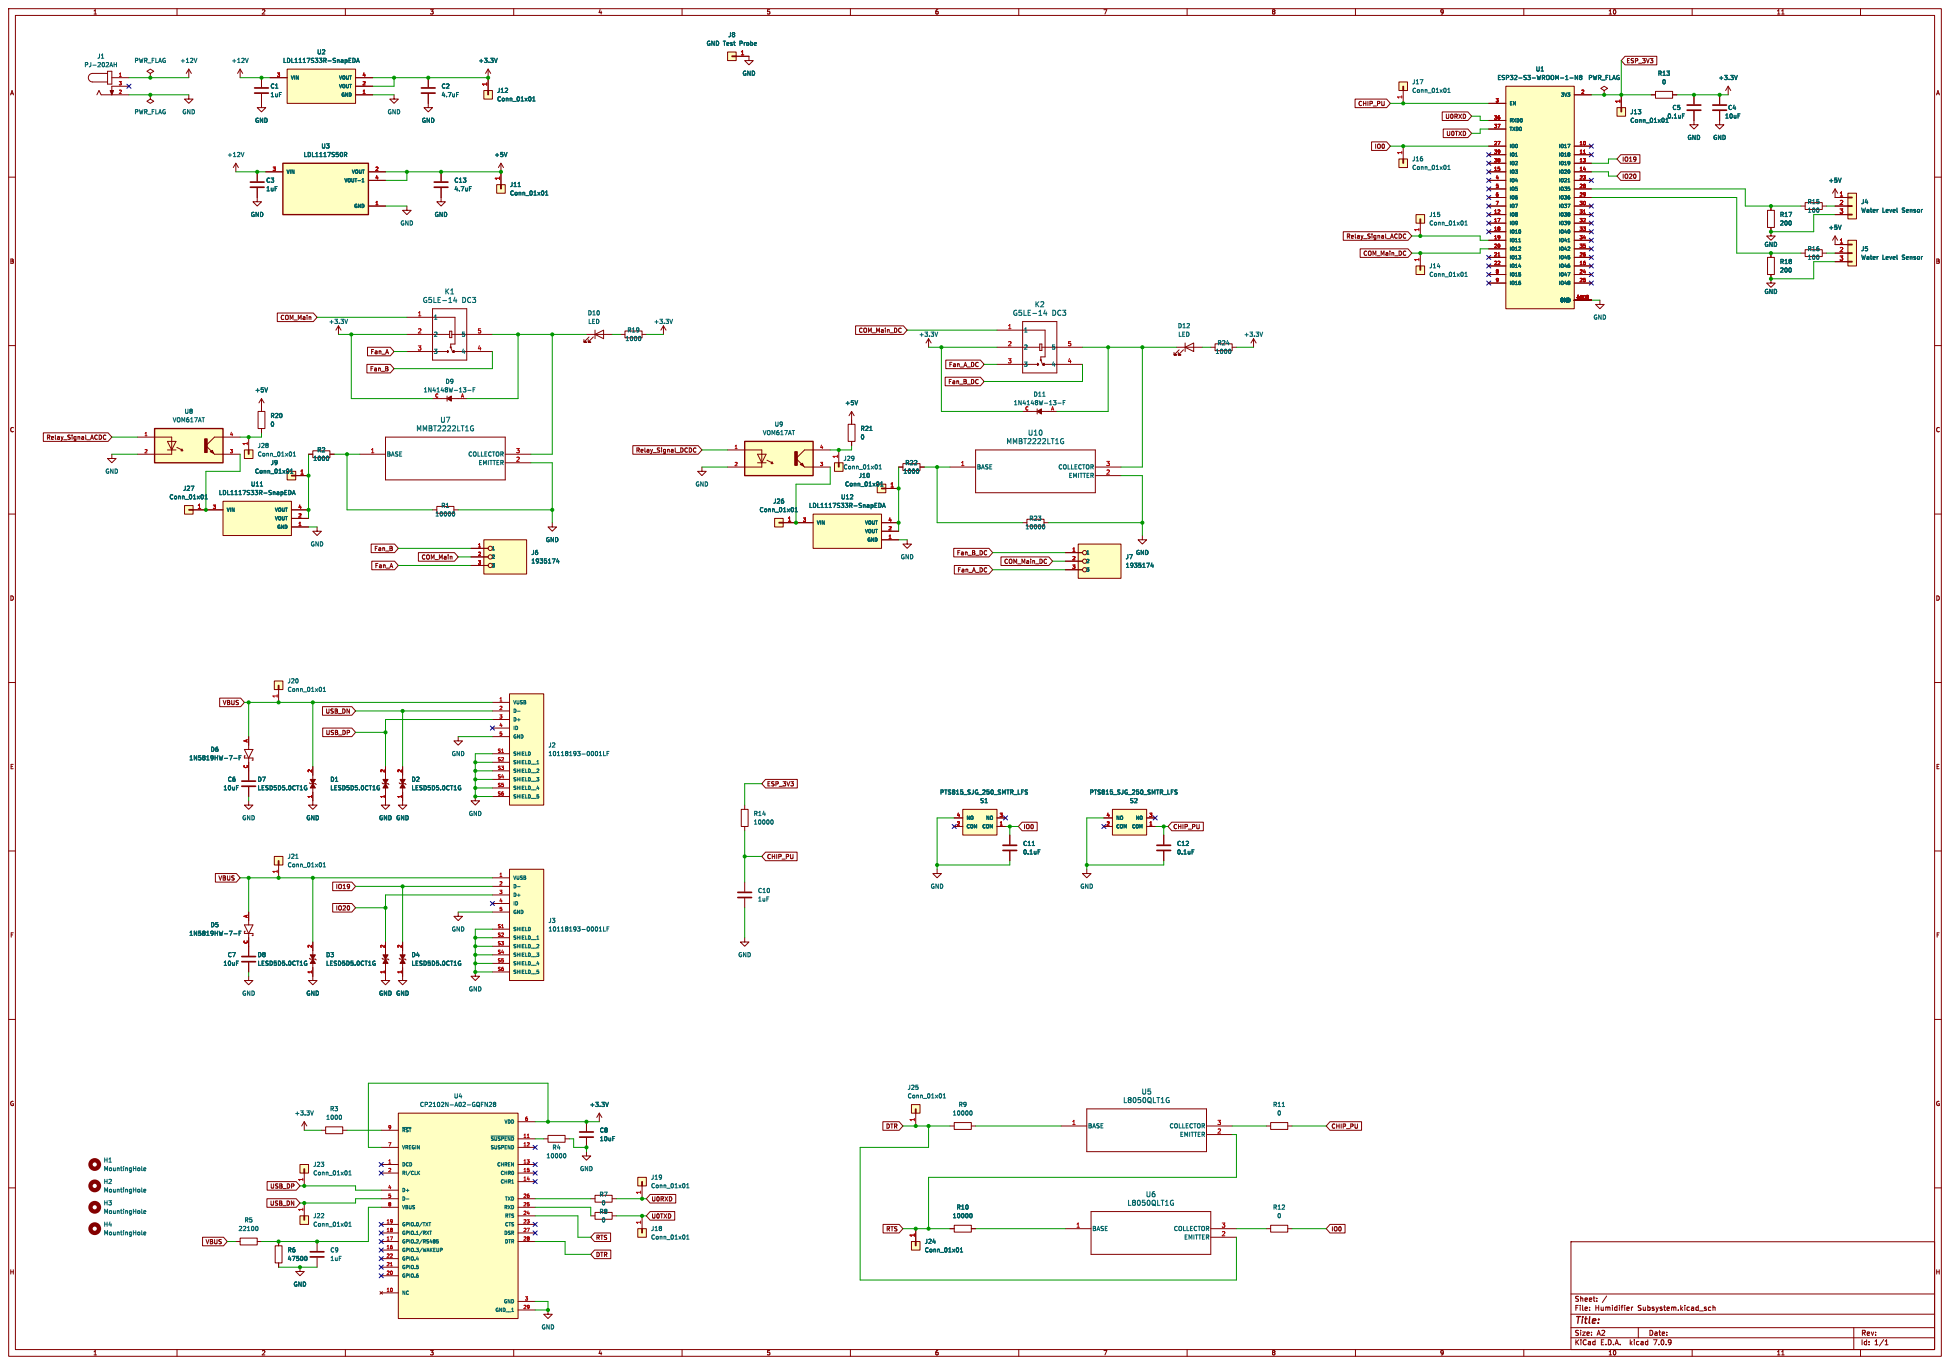
[picture p162: page 1]

H2 MountingHole H1 MountingHole H4 MountingHole H3 MountingHole
