Andrew-Sherwin/ECE445/Course Files/KiCAD Files/Sensor Subsystem/KiCAD7.0/Rev1/Sensor PCB.pdf

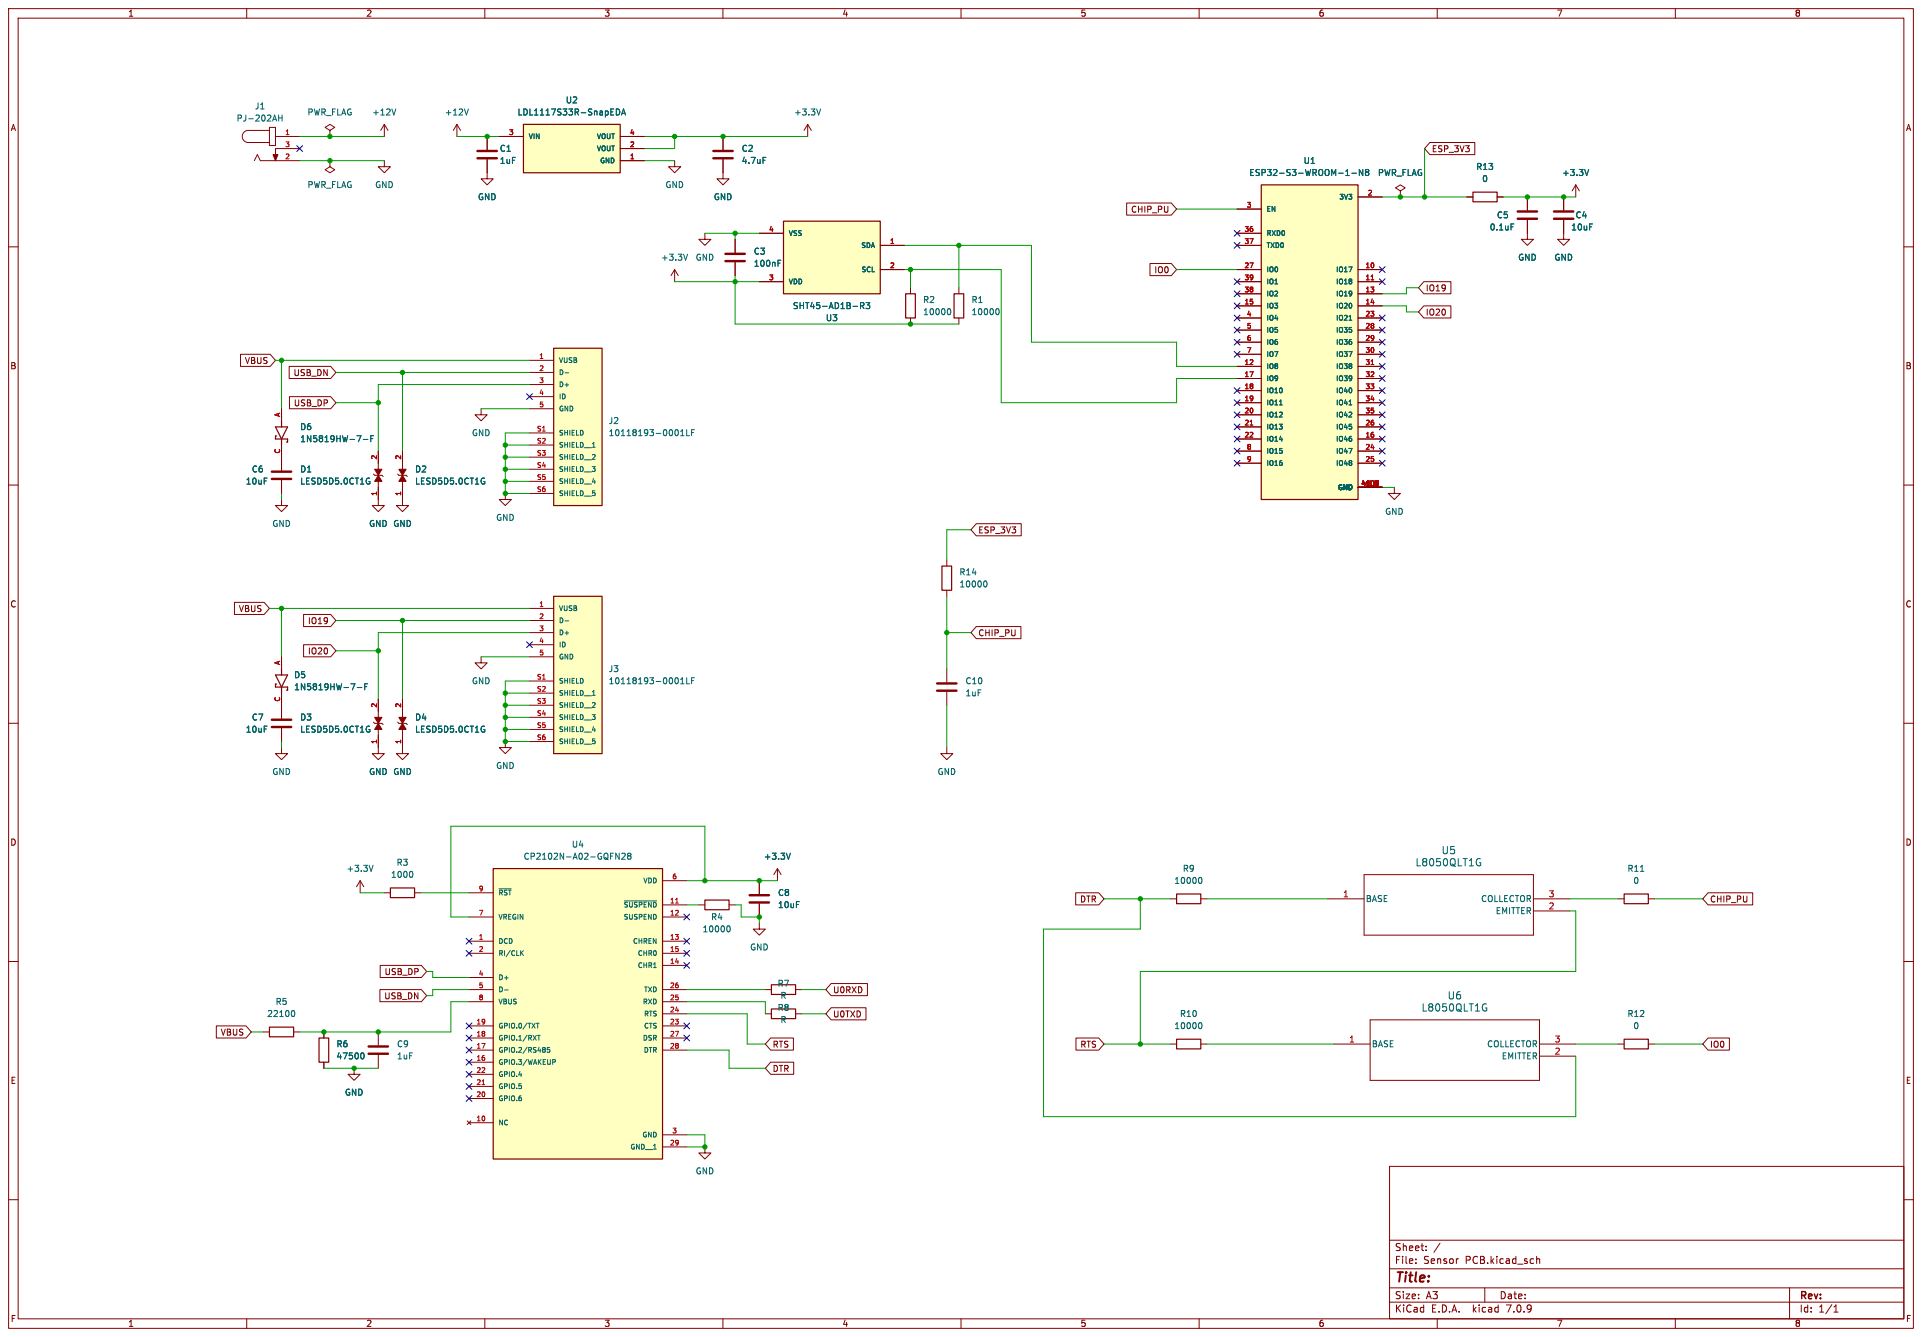
[picture p163: page 1]
