Andrew-Sherwin/ECE445/Course Files/KiCAD Files/Sensor Subsystem/KiCAD7.0/Rev2/Sensor PCB.pdf

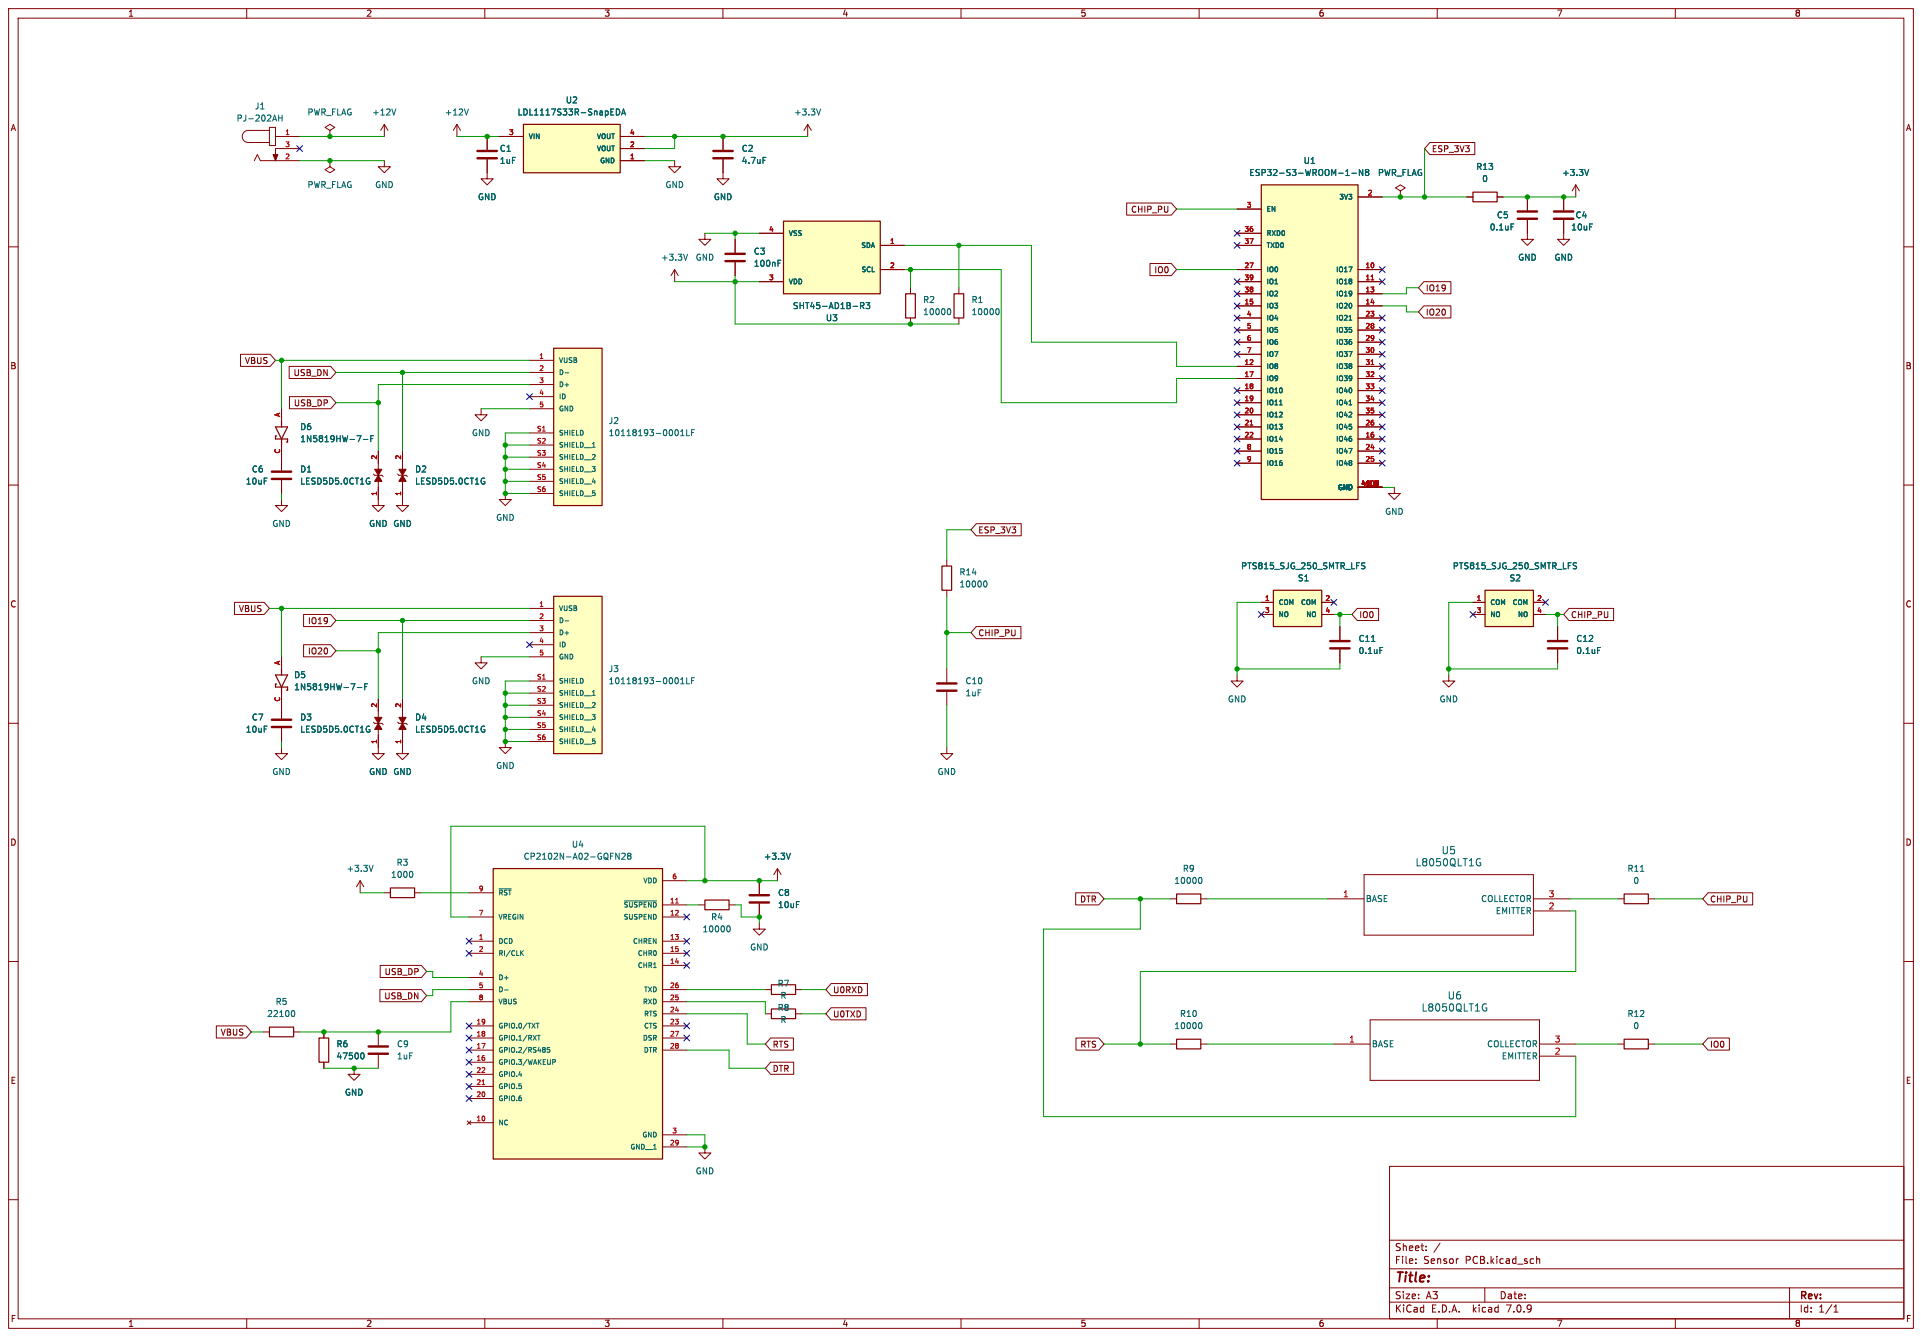
[picture p164: page 1]
