Andrew-Sherwin/ECE445/Course Files/KiCAD Files/Sensor Subsystem/KiCAD7.0/Rev3/Sensor PCB.pdf

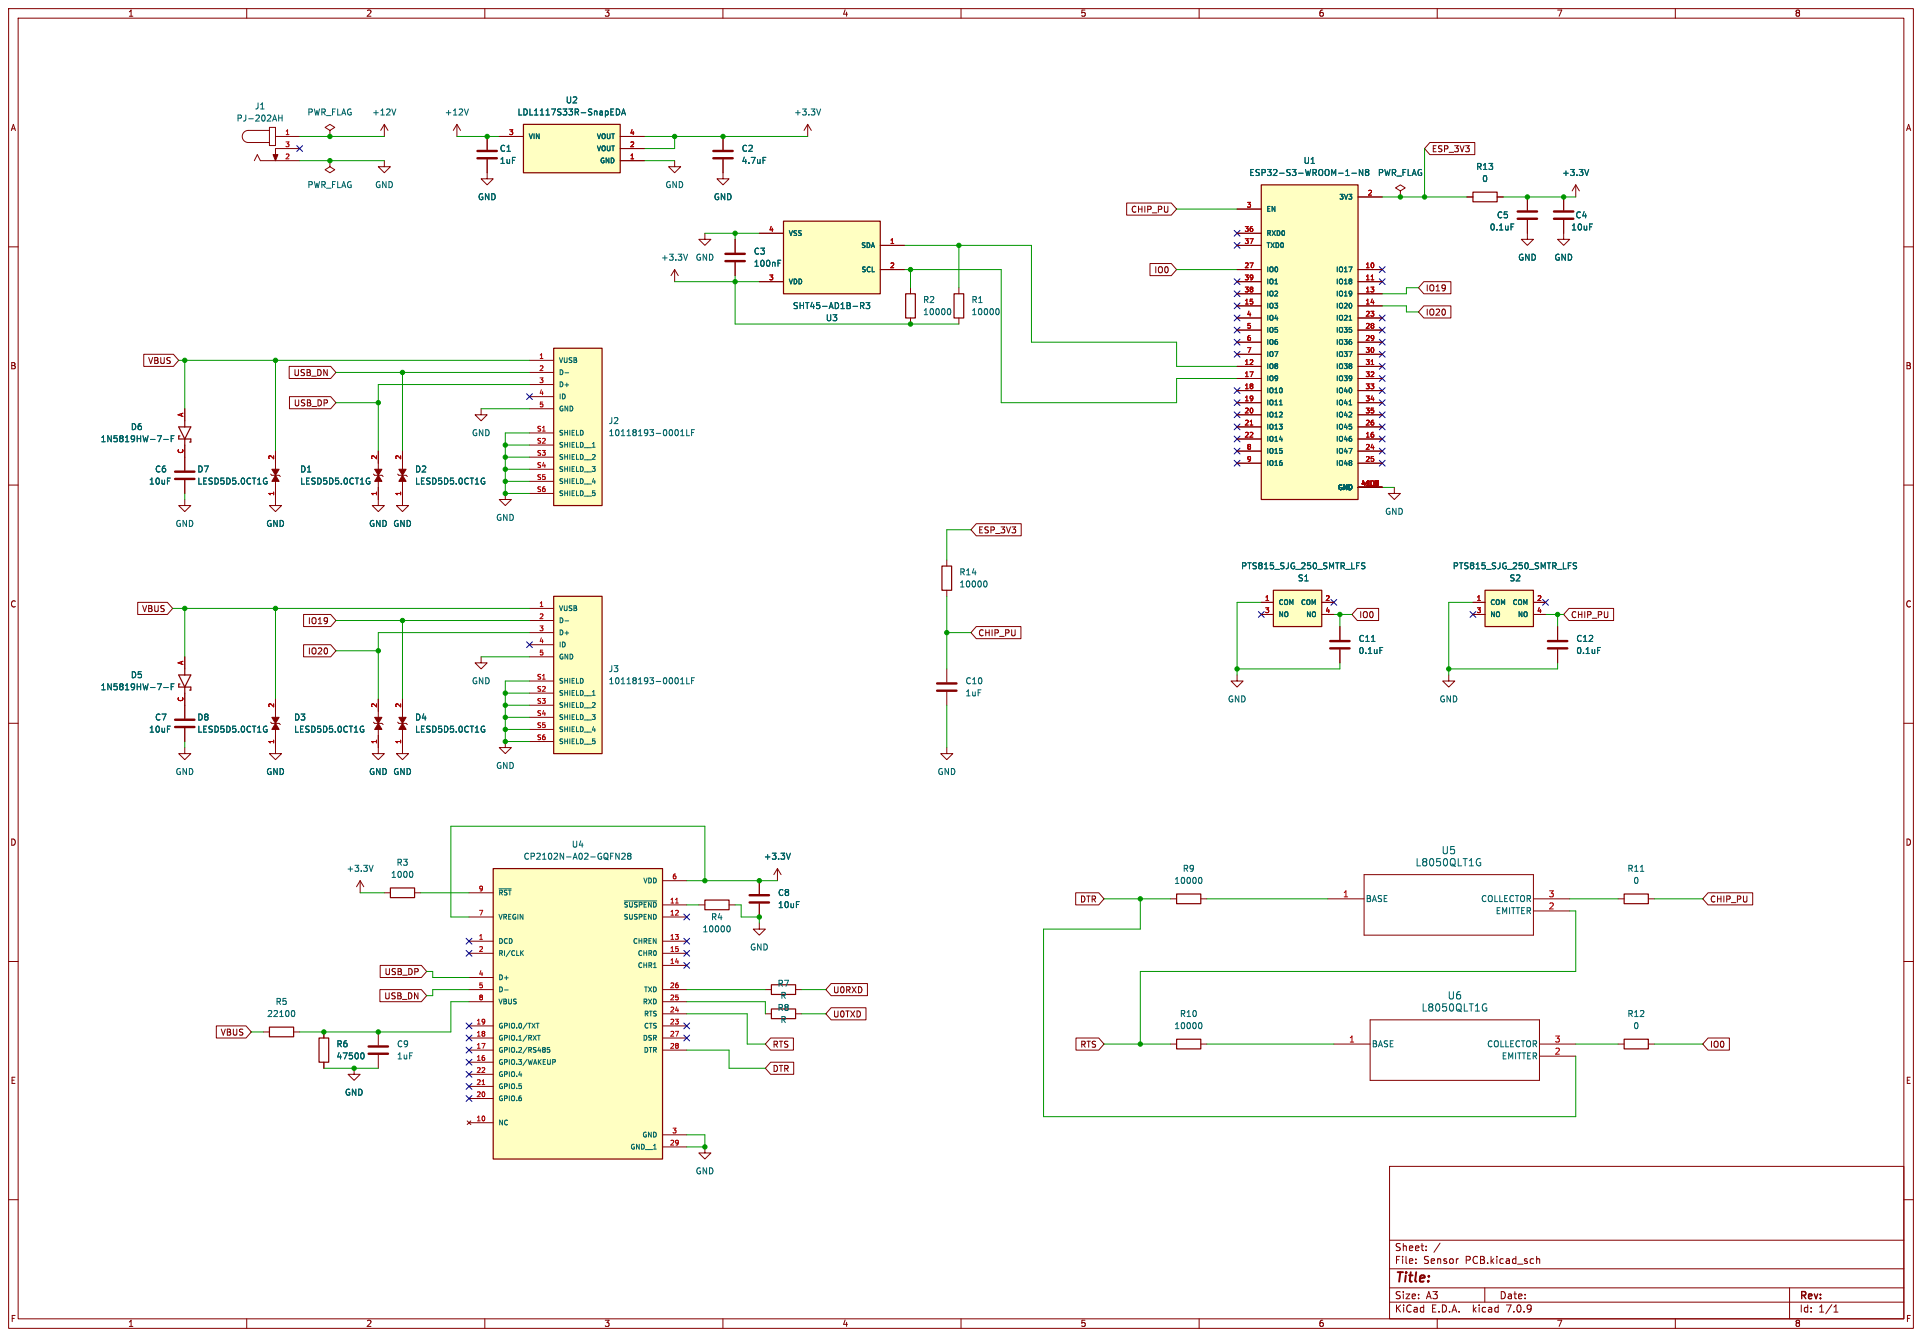
[picture p165: page 1]
