Andrew-Sherwin/ECE445/Course Files/TutorialKiCad/ZYXIE2_miniencabulator/ZYXIE2_miniencabulator.kicad_pcb

## KiCad design Course Files/TutorialKiCad/ZYXIE2_miniencabulator/ZYXIE2_miniencabulator.kicad_pcb (2024-05-02)

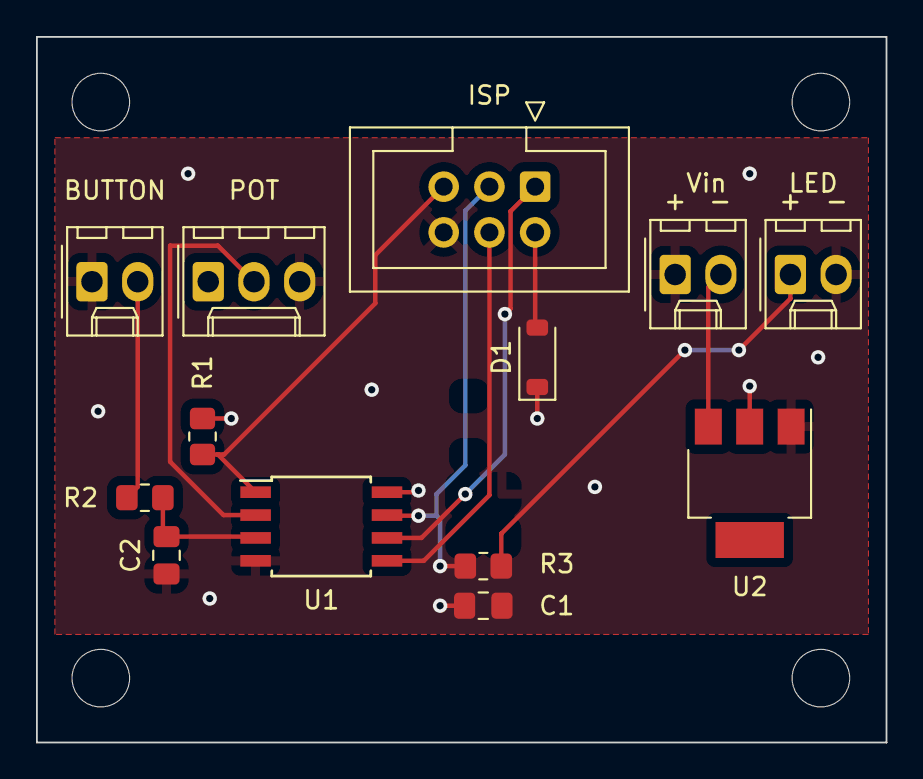
[picture p170: board Course Files/TutorialKiCad/ZYXIE2_miniencabulator/ZYXIE2_miniencabula… from above]

Board: 2 copper layers, 47.2 x 39.2 mm, 17 parts (0 on the bottom side), 12 nets.

Parts:
C1, C2: 1uF; C_0805_2012Metric_Pad1.18x1.45mm_HandSolder
D1: MBR0520; D_SOD-123
H1, H2, H3, H4: MountingHole; MountingHole_3.2mm_M3
J1: ISP; IDC-Header_2x03_P2.54mm_Vertical
J2: Vin; Molex_KK-254_AE-6410-02A_1x02_P2.54mm_Vertical
J3: BUTTON; Molex_KK-254_AE-6410-02A_1x02_P2.54mm_Vertical
J4: POT; Molex_KK-254_AE-6410-03A_1x03_P2.54mm_Vertical
J5: LED; Molex_KK-254_AE-6410-02A_1x02_P2.54mm_Vertical
R1, R2: 10k; R_0805_2012Metric_Pad1.20x1.40mm_HandSolder
R3: 1k; R_0805_2012Metric_Pad1.20x1.40mm_HandSolder
U1: ATtiny85-20S; SOIC-8W_5.3x5.3mm_P1.27mm
U2: LM1117MP-5.0; SOT-223

Connections:
+5V: C1.1, D1.1 (K), J4.1, R1.1, U1.8 (VCC), U2.2 (VO)
/BUTTON: C2.1, R2.1, U1.3 (XTAL2/PB4)
/MISO: J1.1 (MISO), U1.6 (PB1)
/MOSI: J1.4 (MOSI), U1.5 (AREF/PB0)
/RST: J1.5 (~RST), R1.2, U1.1 (~RESET/PB5)
/SCK: J1.3 (SCK), R3.2, U1.7 (PB2)
GND: C1.2, C2.2, J1.6 (GND), J2.1, J3.1, J4.3, J5.2, U1.4 (GND), U2.1 (GND)
unnamed: D1.2 (A), J1.2 (VCC)
unnamed: J2.2, U2.3 (VI)
unnamed: J3.2, R2.2
unnamed: J4.2, U1.2 (XTAL1/PB3)
unnamed: J5.1, R3.1
