Andrew-Sherwin/ECE445/Course Files/KiCAD Files/Humidifier Subsystem/Humidifier PCB/Humidifier PCB.kicad_pcb

## KiCad design Course Files/KiCAD Files/Humidifier Subsystem/Humidifier PCB/Humidifier PCB.kicad_pcb (2024-05-02)

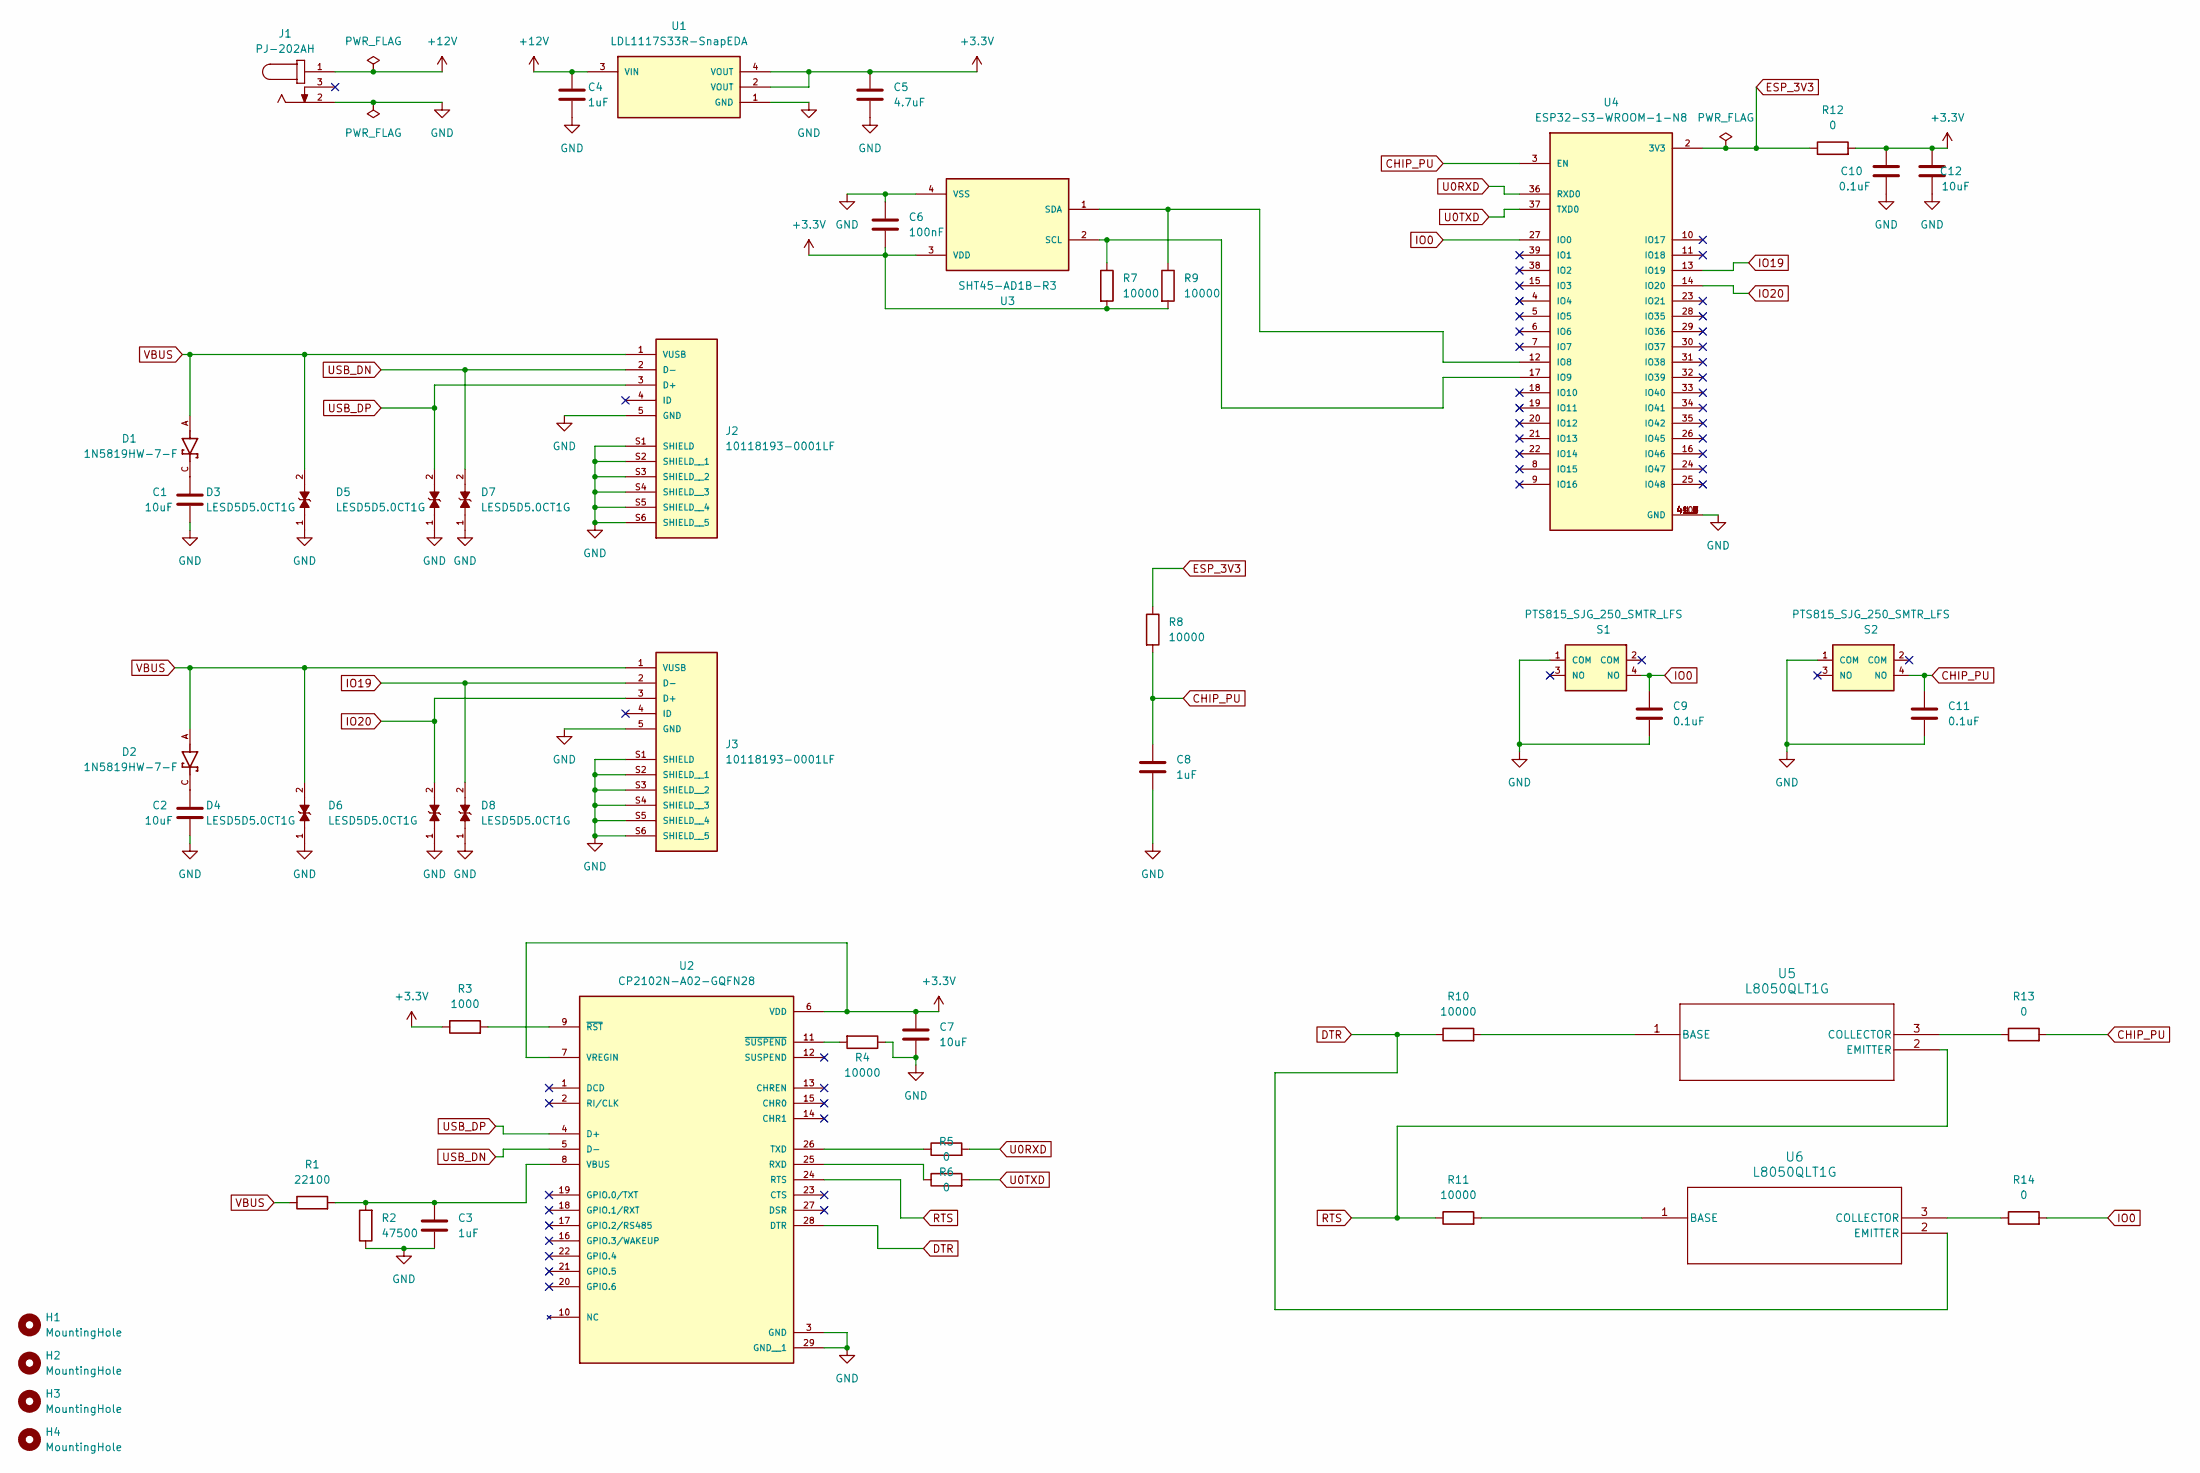
[picture p171: schematic Humidifier PCB.kicad_sch]

Parts:
C1, C2, C7, C12: 10uF
C3, C4, C8: 1uF
C5: 4.7uF
C6: 100nF
C9, C10, C11: 0.1uF
D1, D2: 1N5819HW-7-F; PARTREV 18-2
D3, D4, D5, D6, D7, D8: LESD5D5.0CT1G; PARTREV O
H1, H2, H3, H4: MountingHole
J1: PJ-202AH; PART_REV 1.02
J2, J3: 10118193-0001LF; PARTREV E
R1: 22100
R2: 47500
R3: 1000
R4, R7, R8, R9, R10, R11: 10000
R5, R6, R12, R13, R14: 0
S1, S2: PTS815_SJG_250_SMTR_LFS; MOUSER_PART_NUMBER 611-PTS815SJG250SMTR
U1: LDL1117S33R-SnapEDA; PARTREV 7; DigiKey_Part_Number 497-17239-2-ND
U2: CP2102N-A02-GQFN28; PARTREV 1.5
U3: SHT45-AD1B-R3
U4: ESP32-S3-WROOM-1-N8; DigiKey_Part_Number 1965-ESP32-S3-WROOM-1-N8TR-ND
U5, U6: L8050QLT1G

Connections:
+3.3V: C5.1, C6.2, C7.1, C10.1, C12.1, R3.1, R7.2, R9.2, R12.2, U1.2 (VOUT), U1.4 (VOUT), U2.6 (VDD), U2.7 (VREGIN), U3.3 (VDD)
+12V: C4.1, J1.1, U1.3 (VIN)
CHIP_PU: C8.1, C11.1, R8.2, R13.2, S2.4 (NO), U4.3 (EN)
DTR: R10.1, U2.28 (DTR), U6.2 (EMITTER)
ESP_3V3: R8.1, R12.1, U4.2 (3V3)
GND: C1.2, C2.2, C3.2, C4.2, C5.2, C6.1, C7.2, C8.2, C9.2, C10.2, C11.2, C12.2, D3.1, D4.1, D5.1, D6.1, D7.1, D8.1, J1.2, J2.5 (GND), J2.S1 (SHIELD), J2.S2 (SHIELD__1), J2.S3 (SHIELD__2), J2.S4 (SHIELD__3), J2.S5 (SHIELD__4), J2.S6 (SHIELD__5), J3.5 (GND), J3.S1 (SHIELD), J3.S2 (SHIELD__1), J3.S3 (SHIELD__2), J3.S4 (SHIELD__3), J3.S5 (SHIELD__4), J3.S6 (SHIELD__5), R2.1, R4.1, S1.1 (COM), S2.1 (COM), U1.1 (GND), U2.3 (GND), U2.29 (GND__1), U3.4 (VSS), U4.1 (GND), U4.40 (GND), U4.41_1 (GND), U4.41_2 (GND), U4.41_3 (GND), U4.41_4 (GND), U4.41_5 (GND), U4.41_6 (GND), U4.41_7 (GND), U4.41_8 (GND), U4.41_9 (GND)
IO0: C9.1, R14.2, S1.4 (NO), U4.27 (IO0)
IO19: D8.2, J3.2 (D-), U4.13 (IO19)
IO20: D6.2, J3.3 (D+), U4.14 (IO20)
unnamed: C1.1, D1.C
unnamed: C2.1, D2.C
unnamed: R6.1, U2.25 (RXD)
unnamed: R5.1, U2.26 (TXD)
unnamed: C3.1, R1.2, R2.2, U2.8 (VBUS)
unnamed: R3.2, U2.9 (~RST)
unnamed: R4.2, U2.11 (~SUSPEND)
unnamed: R7.1, U3.2 (SCL), U4.17 (IO9)
unnamed: R9.1, U3.1 (SDA), U4.12 (IO8)
unnamed: R10.2, U5.1 (BASE)
unnamed: R13.1, U5.3 (COLLECTOR)
unnamed: R11.2, U6.1 (BASE)
unnamed: R14.1, U6.3 (COLLECTOR)
RTS: R11.1, U2.24 (RTS), U5.2 (EMITTER)
U0RXD: R5.2, U4.36 (RXD0)
U0TXD: R6.2, U4.37 (TXD0)
USB_DN: D7.2, J2.2 (D-), U2.5 (D-)
USB_DP: D5.2, J2.3 (D+), U2.4 (D+)
VBUS: D1.A, D2.A, D3.2, D4.2, J2.1 (VUSB), J3.1 (VUSB), R1.1

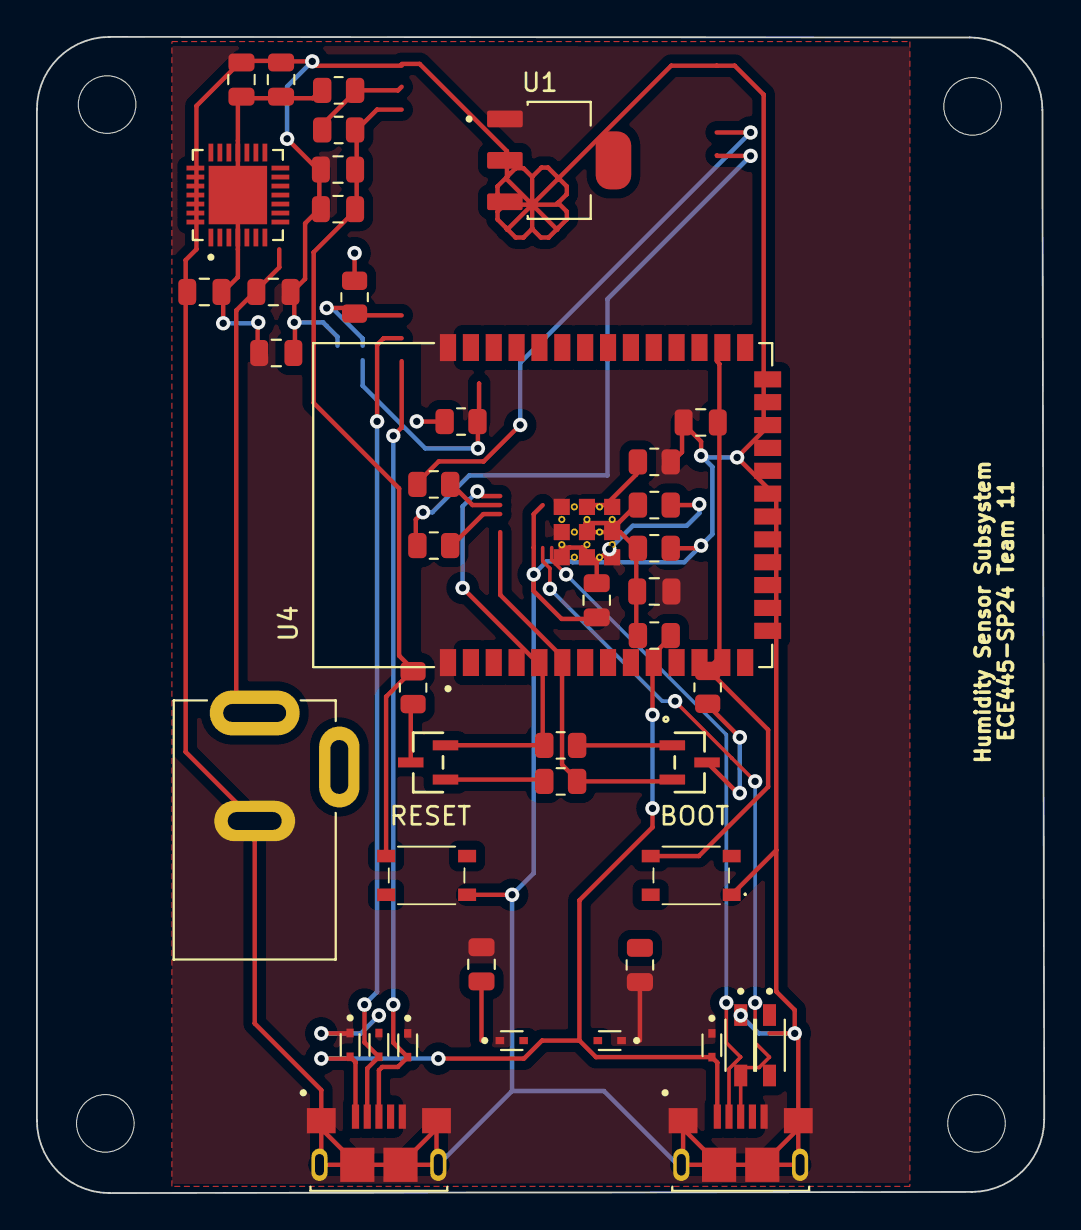
[picture p172: board Course Files/KiCAD Files/Humidifier Subsystem/Humidifier PCB/Humidifi… from above]

Board: 2 copper layers, 56.0 x 64.2 mm, 49 parts (1 on the bottom side), 28 nets.
