Andrew-Sherwin/ECE445/Course Files/TutorialKiCad/ZYXIE2_miniencabulator/Rev0/ZYXIE2_miniencabulator.kicad_pcb

## KiCad design Course Files/TutorialKiCad/ZYXIE2_miniencabulator/Rev0/ZYXIE2_miniencabulator.kicad_pcb (2024-05-02)

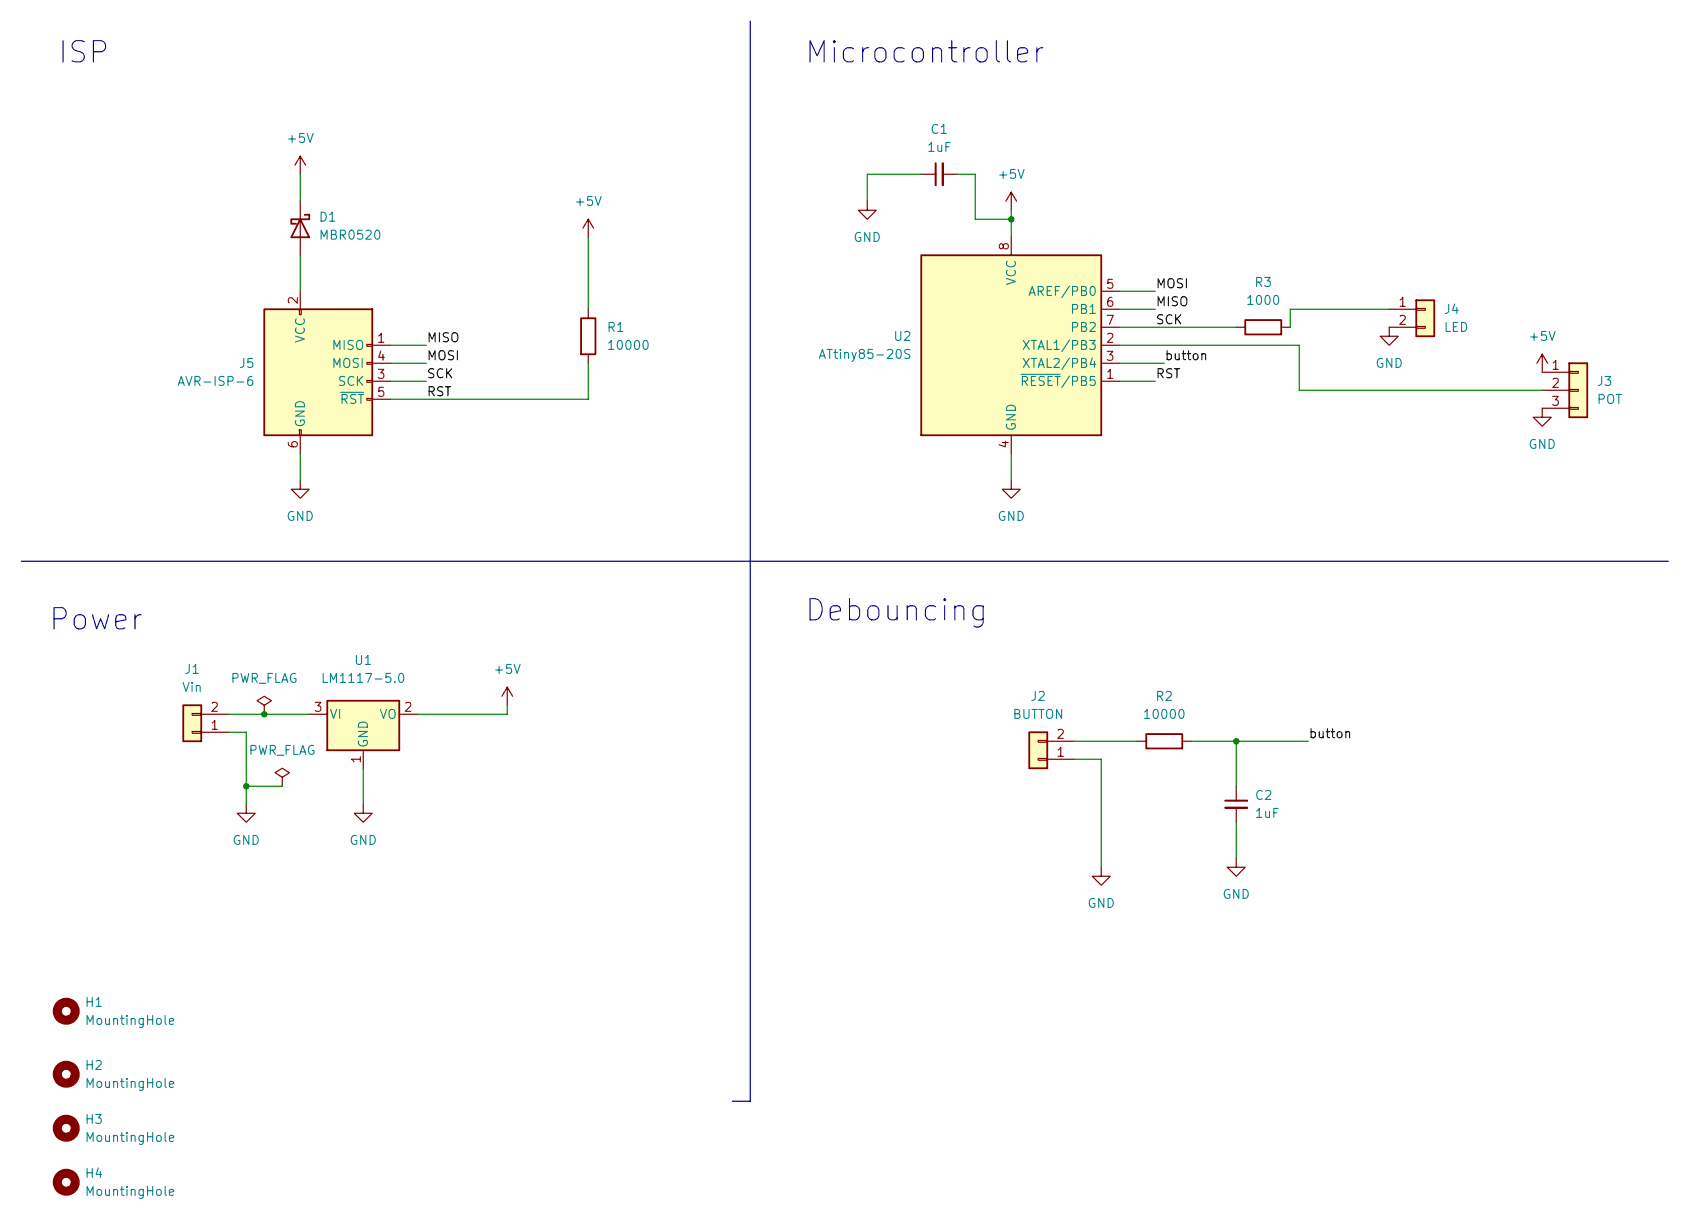
[picture p173: schematic ZYXIE2_miniencabulator.kicad_sch]

Parts:
C1, C2: 1uF; C_0805_2012Metric_Pad1.18x1.45mm_HandSolder
D1: MBR0520; D_SOD-123
H1, H2, H3, H4: MountingHole; MountingHole_3.2mm_M3
J1: Vin; Molex_KK-254_AE-6410-02A_1x02_P2.54mm_Vertical
J2: BUTTON; Molex_KK-254_AE-6410-02A_1x02_P2.54mm_Vertical
J3: POT; Molex_KK-254_AE-6410-03A_1x03_P2.54mm_Vertical
J4: LED; Molex_KK-254_AE-6410-02A_1x02_P2.54mm_Vertical
J5: AVR-ISP-6; IDC-Header_2x03_P2.54mm_Vertical
R1, R2: 10000; R_0805_2012Metric_Pad1.20x1.40mm_HandSolder
R3: 1000; R_0805_2012Metric_Pad1.20x1.40mm_HandSolder
U1: LM1117-5.0; SOT-223
U2: ATtiny85-20S; SOIC-8W_5.3x5.3mm_P1.27mm

Connections:
+5V: C1.2, D1.1 (K), J3.1, R1.1, U1.2 (VO), U2.8 (VCC)
/MISO: J5.1 (MISO), U2.6 (PB1)
/MOSI: J5.4 (MOSI), U2.5 (AREF/PB0)
/RST: J5.5 (~RST), R1.2, U2.1 (~RESET/PB5)
/SCK: J5.3 (SCK), R3.1, U2.7 (PB2)
/button: C2.1, R2.2, U2.3 (XTAL2/PB4)
GND: C1.1, C2.2, J1.1, J2.1, J3.3, J4.2, J5.6 (GND), U1.1 (GND), U2.4 (GND)
unnamed: D1.2 (A), J5.2 (VCC)
unnamed: J3.2, U2.2 (XTAL1/PB3)
unnamed: J2.2, R2.1
unnamed: J4.1, R3.2
unnamed: J1.2, U1.3 (VI)

Notes on the sheet:
Debouncing
ISP
Microcontroller
Power

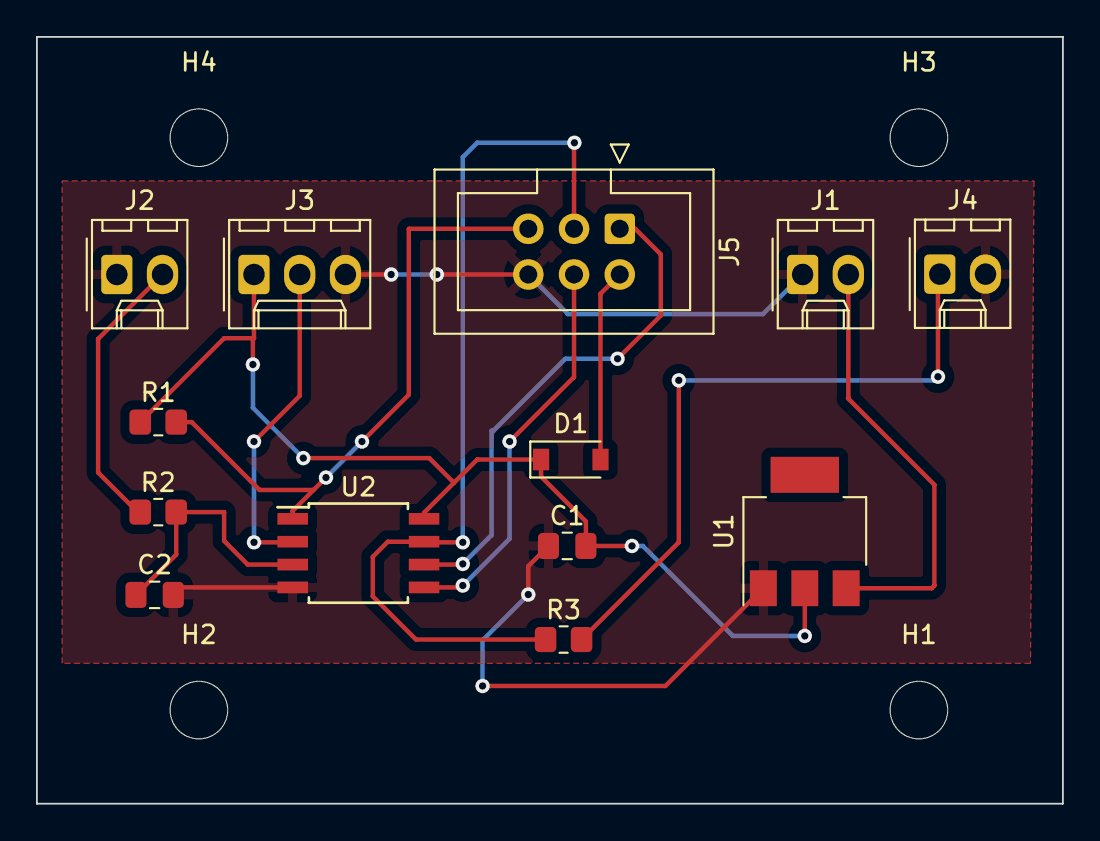
[picture p174: board Course Files/TutorialKiCad/ZYXIE2_miniencabulator/Rev0/ZYXIE2_minienc… from above]

Board: 2 copper layers, 57.0 x 42.6 mm, 17 parts (0 on the bottom side), 12 nets.
